rgregg/esp32-wireless-thermostat/src/controller/controller_runtime.cpp

#include "controller/controller_runtime.h"

#include <stdarg.h>
#include <stdio.h>
#include <string.h>

#include "controller/audit_log.h"
#include "espnow_cmd_word.h"
#include "mqtt_payload.h"
#include "thermostat/thermostat_state.h"

namespace {

constexpr uint32_t kOneMinuteMs = 60000;

}  // namespace

namespace thermostat {

static const char *hvac_state_str(ControllerRuntime::HvacState s) {
  switch (s) {
    case ControllerRuntime::HvacState::Idle: return "idle";
    case ControllerRuntime::HvacState::Heating: return "heating";
    case ControllerRuntime::HvacState::Cooling: return "cooling";
    default: return "?";
  }
}

void ControllerRuntime::audit(const char *fmt, ...) const {
  if (!audit_cb_) return;
  char buf[80];
  va_list ap;
  va_start(ap, fmt);
  vsnprintf(buf, sizeof(buf), fmt, ap);
  va_end(ap);
  audit_cb_(buf);
}

ControllerRuntime::ControllerRuntime(const ControllerConfig &config)
    : config_(config) {
  last_heating_off_ms_ = 0;
  last_cooling_off_ms_ = 0;
  hvac_state_since_ms_ = 0;
}

void ControllerRuntime::note_heartbeat(uint32_t now_ms) {
  heartbeat_last_seen_ms_ = now_ms;
}

void ControllerRuntime::set_hvac_lockout(bool locked_out) {
  if (locked_out != hvac_lockout_) {
    audit("lockout: %s [internal]", locked_out ? "on" : "off");
  }
  hvac_lockout_ = locked_out;
  if (hvac_lockout_) {
    hvac_state_ = HvacState::Idle;
    relay_.fan = false;
    relay_.heat = false;
    relay_.cool = false;
  }
}

void ControllerRuntime::set_windows_open(bool open) {
  if (open != windows_open_) {
    audit("windows_open: %s [internal]", open ? "on" : "off");
  }
  windows_open_ = open;
}

void ControllerRuntime::reset_remote_command_sequence() {
  last_seq_default_ = 0;
  for (int i = 0; i < kMaxCommandSources; ++i) {
    command_sources_[i].active = false;
    command_sources_[i].last_seq = 0;
  }
}

CommandApplyResult ControllerRuntime::apply_remote_command(const CommandWord &cmd,
                                                           const uint8_t *source_mac) {
  CommandApplyResult result;

  // Resolve the per-source sequence counter
  uint16_t *last_seq = &last_seq_default_;

  if (source_mac != nullptr) {
    // Find existing entry or allocate a new one
    int free_slot = -1;
    for (int i = 0; i < kMaxCommandSources; ++i) {
      if (command_sources_[i].active &&
          memcmp(command_sources_[i].mac, source_mac, 6) == 0) {
        last_seq = &command_sources_[i].last_seq;
        free_slot = -2;  // sentinel: found
        break;
      }
      if (!command_sources_[i].active && free_slot == -1) {
        free_slot = i;
      }
    }
    if (free_slot >= 0) {
      // New source — register it
      memcpy(command_sources_[free_slot].mac, source_mac, 6);
      command_sources_[free_slot].last_seq = 0;
      command_sources_[free_slot].active = true;
      last_seq = &command_sources_[free_slot].last_seq;
    } else if (free_slot == -1) {
      // All slots full and source not found — reject to avoid
      // sharing sequence tracking with the default source
      result.stale_or_duplicate = true;
      return result;
    }
  }

  if (*last_seq != 0) {
    if (!espnow_cmd::is_newer_seq(*last_seq, cmd.seq)) {
      result.stale_or_duplicate = true;
      return result;
    }
  }

  *last_seq = cmd.seq;
  result.accepted = true;

  if (cmd.sync_request) {
    result.sync_requested = true;
    return result;
  }

  const FurnaceMode old_mode = mode_;
  const FanMode old_fan = fan_mode_;
  const float old_setpoint = target_temperature_c();

  if (!cmd.preserve_mode) {
    mode_ = cmd.mode;
  }
  if (!cmd.preserve_fan) {
    fan_mode_ = cmd.fan;
  }
  // Route the incoming setpoint into the bin matching the resolved mode (the
  // mode we'll be in after applying this command). For Off, leave both bins
  // unchanged so a mode-only switch doesn't clobber the stored targets.
  // preserve_setpoint suppresses any bin update entirely.
  if (!cmd.preserve_setpoint) {
    const float incoming_sp = static_cast<float>(cmd.setpoint_decic) / 10.0f;
    const FurnaceMode bin_mode = cmd.preserve_mode ? mode_ : cmd.mode;
    if (bin_mode == FurnaceMode::Heat) {
      heat_setpoint_c_ = incoming_sp;
    } else if (bin_mode == FurnaceMode::Cool) {
      cool_setpoint_c_ = incoming_sp;
    }
  }

  // Audit changes with source MAC when available
  char src_str[32];
  if (source_mac) {
    char mac_buf[18];
    format_mac(mac_buf, sizeof(mac_buf), source_mac);
    snprintf(src_str, sizeof(src_str), "espnow %s", mac_buf);
  } else {
    strcpy(src_str, "mqtt");
  }
  if (mode_ != old_mode) {
    audit("mode: %s->%s [%s]",
          mqtt_payload::mode_to_str(old_mode),
          mqtt_payload::mode_to_str(mode_), src_str);
    // Clear sticky max-runtime flag when user changes mode (acknowledgment)
    if (max_runtime_exceeded_) {
      max_runtime_exceeded_ = false;
      audit("max_runtime: cleared by mode change [internal]");
    }
  }
  if (fan_mode_ != old_fan) {
    audit("fan: %s->%s [%s]",
          mqtt_payload::fan_to_str(old_fan),
          mqtt_payload::fan_to_str(fan_mode_), src_str);
  }
  const float new_setpoint = target_temperature_c();
  if (new_setpoint != old_setpoint) {
    audit("setpoint: %.1f->%.1f [%s]",
          static_cast<double>(old_setpoint),
          static_cast<double>(new_setpoint), src_str);
  }

  if (cmd.filter_reset) {
    filter_runtime_seconds_ = 0;
    result.filter_reset_requested = true;
    audit("filter_reset [%s]", src_str);
  }

  return result;
}

void ControllerRuntime::tick(const ControllerTickInput &in) {
  update_failsafe(in.now_ms, in.has_indoor_temp);
  apply_hvac_calls(in.now_ms, in.heat_call, in.cool_call);
  run_minute_tasks(in.now_ms);
  enforce_safety_interlocks(in.now_ms);
}

float ControllerRuntime::target_temperature_c() const {
  // Cool mode reports cool bin; Heat and Off both report heat bin.
  // Off's value is informational only — HVAC logic is gated on mode anyway.
  if (mode_ == FurnaceMode::Cool) return cool_setpoint_c_;
  return heat_setpoint_c_;
}

FurnaceStateCode ControllerRuntime::furnace_state() const {
  FurnaceStateCode base = compute_furnace_state(snapshot());
  if (equipment_delay_) {
    if (base == FurnaceStateCode::HeatMode) return FurnaceStateCode::HeatWait;
    if (base == FurnaceStateCode::CoolMode) return FurnaceStateCode::CoolWait;
  }
  return base;
}

ThermostatSnapshot ControllerRuntime::snapshot() const {
  ThermostatSnapshot s;
  s.mode = mode_;
  s.fan_mode = fan_mode_;
  s.relay = relay_;
  s.hvac_lockout = hvac_lockout_;
  s.failsafe_active = failsafe_active_;
  s.windows_open = windows_open_;
  return s;
}

void ControllerRuntime::enforce_safety_interlocks(uint32_t now_ms) {
  if (failsafe_active_ || hvac_lockout_) {
    enter_idle(now_ms);
    relay_.fan = false;
  }

  if (relay_.heat) {
    relay_.cool = false;
    relay_.fan = false;
  } else if (relay_.cool) {
    relay_.heat = false;
    relay_.fan = false;
  }
}

void ControllerRuntime::update_failsafe(uint32_t now_ms, bool has_indoor_temp) {
  const bool was_active = failsafe_active_;
  failsafe_active_ = !has_indoor_temp ||
                     is_failsafe_timed_out(now_ms, heartbeat_last_seen_ms_,
                                           config_.failsafe_timeout_ms);
  if (failsafe_active_ != was_active) {
    if (failsafe_active_) {
      audit("failsafe: on (%s) [internal]",
            !has_indoor_temp ? "no indoor temp" : "heartbeat timeout");
    } else {
      audit("failsafe: off [internal]");
    }
  }
}

void ControllerRuntime::apply_hvac_calls(uint32_t now_ms, bool heat_call, bool cool_call) {
  if (failsafe_active_ || hvac_lockout_) {
    enter_idle(now_ms);
    relay_.fan = false;
    equipment_delay_ = false;
    return;
  }

  if (windows_open_) {
    cool_call = false;
  }

  switch (hvac_state_) {
    case HvacState::Heating: {
      const bool min_run_done =
          elapsed_at_least(now_ms, hvac_state_since_ms_, config_.min_heating_run_time_ms);
      const bool max_run_exceeded =
          config_.max_heating_run_time_ms > 0 &&
          elapsed_at_least(now_ms, hvac_state_since_ms_, config_.max_heating_run_time_ms);
      if (max_run_exceeded) {
        audit("heating: max runtime exceeded, forcing idle [internal]");
        max_runtime_exceeded_ = true;
        enter_idle(now_ms);
      } else if (!heat_call && min_run_done) {
        enter_idle(now_ms);
      } else {
        relay_.heat = true;
        relay_.cool = false;
      }
      break;
    }
    case HvacState::Cooling: {
      const bool min_run_done =
          elapsed_at_least(now_ms, hvac_state_since_ms_, config_.min_cooling_run_time_ms);
      const bool max_run_exceeded =
          config_.max_cooling_run_time_ms > 0 &&
          elapsed_at_least(now_ms, hvac_state_since_ms_, config_.max_cooling_run_time_ms);
      if (max_run_exceeded) {
        audit("cooling: max runtime exceeded, forcing idle [internal]");
        max_runtime_exceeded_ = true;
        enter_idle(now_ms);
      } else if (!cool_call && min_run_done) {
        enter_idle(now_ms);
      } else {
        relay_.heat = false;
        relay_.cool = true;
      }
      break;
    }
    case HvacState::Idle:
    default: {
      const bool idle_ready = elapsed_at_least(now_ms, hvac_state_since_ms_, config_.min_idle_time_ms);
      const bool heat_off_ready =
          !has_heating_off_timestamp_ ||
          elapsed_at_least(now_ms, last_heating_off_ms_, config_.min_heating_off_time_ms);
      const bool cool_off_ready =
          !has_cooling_off_timestamp_ ||
          elapsed_at_least(now_ms, last_cooling_off_ms_, config_.min_cooling_off_time_ms);

      if (heat_call && idle_ready && heat_off_ready) {
        enter_heating(now_ms);
      } else if (cool_call && idle_ready && cool_off_ready) {
        enter_cooling(now_ms);
      } else {
        relay_.heat = false;
        relay_.cool = false;
        equipment_delay_ = (heat_call && (!idle_ready || !heat_off_ready)) ||
                           (cool_call && (!idle_ready || !cool_off_ready));
      }
      break;
    }
  }

  if (fan_mode_ == FanMode::AlwaysOn && !spare_relay_4_) {
    relay_.fan = true;
  } else if (fan_mode_ != FanMode::Circulate) {
    relay_.fan = false;
  }
}

void ControllerRuntime::run_minute_tasks(uint32_t now_ms) {
  if (last_minute_tick_ms_ == 0) {
    last_minute_tick_ms_ = now_ms;
    return;
  }

  while (elapsed_at_least(now_ms, last_minute_tick_ms_, kOneMinuteMs)) {
    last_minute_tick_ms_ += kOneMinuteMs;

    if (relay_.heat || relay_.cool || relay_.fan || spare_relay_4_) {
      filter_runtime_seconds_ += 60;
    }

    if (!failsafe_active_ && !hvac_lockout_ && fan_mode_ == FanMode::Circulate) {
      const int period = static_cast<int>(config_.fan_circulate_period_min);
      const int duration = static_cast<int>(config_.fan_circulate_duration_min);
      if (period > 0 && duration > 0) {
        ++fan_circulate_elapsed_min_;
        const bool window_open = (fan_circulate_elapsed_min_ % period) < duration;
        if (window_open && !relay_.heat && !relay_.cool && !spare_relay_4_) {
          relay_.fan = true;
        } else {
          relay_.fan = false;
        }
      }
    } else {
      fan_circulate_elapsed_min_ = 0;
    }
  }
}

bool ControllerRuntime::elapsed_at_least(uint32_t now_ms,
                                         uint32_t start_ms,
                                         uint32_t duration_ms) const {
  if (duration_ms == 0) {
    return true;
  }
  return static_cast<uint32_t>(now_ms - start_ms) >= duration_ms;
}

void ControllerRuntime::enter_idle(uint32_t now_ms) {
  if (hvac_state_ != HvacState::Idle) {
    audit("furnace: %s->idle [internal]", hvac_state_str(hvac_state_));
  }
  if (hvac_state_ == HvacState::Heating) {
    last_heating_off_ms_ = now_ms;
    has_heating_off_timestamp_ = true;
  } else if (hvac_state_ == HvacState::Cooling) {
    last_cooling_off_ms_ = now_ms;
    has_cooling_off_timestamp_ = true;
  }

  hvac_state_ = HvacState::Idle;
  hvac_state_since_ms_ = now_ms;
  relay_.heat = false;
  relay_.cool = false;
}

void ControllerRuntime::enter_heating(uint32_t now_ms) {
  audit("furnace: %s->heating [internal]", hvac_state_str(hvac_state_));
  hvac_state_ = HvacState::Heating;
  hvac_state_since_ms_ = now_ms;
  relay_.heat = true;
  relay_.cool = false;
  relay_.fan = false;
  equipment_delay_ = false;
  max_runtime_exceeded_ = false;
}

void ControllerRuntime::enter_cooling(uint32_t now_ms) {
  audit("furnace: %s->cooling [internal]", hvac_state_str(hvac_state_));
  hvac_state_ = HvacState::Cooling;
  hvac_state_since_ms_ = now_ms;
  relay_.heat = false;
  relay_.cool = true;
  relay_.fan = false;
  equipment_delay_ = false;
  max_runtime_exceeded_ = false;
}

}  // namespace thermostat
