rgregg/esp32-wireless-thermostat/src/thermostat/esp32s3_thermostat_firmware.cpp

#if defined(ARDUINO) && defined(THERMOSTAT_ROLE_THERMOSTAT)

#include "thermostat/esp32s3_thermostat_firmware.h"

#include <atomic>
#include <cctype>
#include <cmath>
#include <cstring>
#include <ctime>
#include <cstdio>

#include <Wire.h>
#include <lvgl.h>
#include <ESPmDNS.h>
#include <Preferences.h>
#include <WiFi.h>
#include "wifi_provisioning_manager.h"
#include <PubSubClient.h>
#include <WebServer.h>
#include <HTTPClient.h>
#include <WiFiClientSecure.h>
#include <esp_mac.h>
#include <esp_system.h>
#include "ota_web_updater.h"
#include "web/web_ui_escape.h"
#include "web/web_ui_shell.h"
#include "web/web_ui_fields.h"

#include "thermostat/thermostat_device_runtime.h"
#include "mqtt_payload.h"
#include "mqtt_topics.h"
#include "wifi_watchdog.h"
#include "weather_icon.h"
#include "thermostat/thermostat_screen_controller.h"
#include "thermostat/ui/thermostat_ui_shared.h"
#include "management_paths.h"
#include "device_registry.h"
#include "mac_address_utils.h"

#include <Adafruit_AHTX0.h>
#include <Adafruit_Si7021.h>

#include "esp_heap_caps.h"
#include "esp_lcd_panel_ops.h"
#include "esp_lcd_panel_rgb.h"
#include "esp_task_wdt.h"
#include "freertos/FreeRTOS.h"
#include "freertos/semphr.h"

namespace thermostat {
namespace {

constexpr int kDisplayWidth = 800;
constexpr int kDisplayHeight = 480;
constexpr uint32_t kUiTickMs = 5;
constexpr uint32_t kRuntimeTickMs = 200;
constexpr uint32_t kSensorPollMs = 60000;
constexpr uint32_t kUiRefreshMs = 500;

constexpr int kBacklightPin = 2;
// The backlight driver needs ~30 us per enable pulse to start, so ultrasonic
// PWM can't dim (25 kHz was black below ~80% duty). 800 Hz whined audibly at
// screensaver brightness; 250 Hz sits where the ear is far less sensitive.
constexpr int kBacklightFreq = 250;
constexpr int kBacklightResolution = 8;

constexpr uint8_t kGt911Addr = 0x5D;

constexpr int kTouchI2cSda = 19;
constexpr int kTouchI2cScl = 20;
constexpr int kTouchRstPin = 38;
constexpr int kSensorI2cSda = 18;
constexpr int kSensorI2cScl = 17;
constexpr uint32_t kNetworkRetryMs = 5000;
constexpr uint32_t kMqttPublishMs = 10000;
constexpr uint32_t kDisplayInitSettleMs = 150;
constexpr uint32_t kBacklightEnableDelayMs = 400;
constexpr uint32_t kRebootDelayMs = 1000;
constexpr uint32_t kRebootPanelOffDelayMs = 200;
constexpr uint32_t kIsolationRebootMs = 15UL * 60UL * 1000UL;

#ifndef THERMOSTAT_WIFI_SSID
#define THERMOSTAT_WIFI_SSID ""
#endif

#ifndef THERMOSTAT_WIFI_PASSWORD
#define THERMOSTAT_WIFI_PASSWORD ""
#endif

// ESP-NOW-only mode: when 1, the display never joins WiFi and never enters BLE
// provisioning — it brings up the LCD + ESP-NOW only. Useful for a display that
// talks solely to the controller over ESP-NOW (no WiFi infrastructure), and for
// bench validation where WiFi association would fight the pinned ESP-NOW channel.
#ifndef THERMOSTAT_WIFI_DISABLED
#define THERMOSTAT_WIFI_DISABLED 0
#endif

#ifndef THERMOSTAT_MQTT_HOST
#define THERMOSTAT_MQTT_HOST "mqtt.lan"
#endif

#ifndef THERMOSTAT_MQTT_PORT
#define THERMOSTAT_MQTT_PORT 1883
#endif

#ifndef THERMOSTAT_MQTT_USER
#define THERMOSTAT_MQTT_USER ""
#endif

#ifndef THERMOSTAT_MQTT_PASSWORD
#define THERMOSTAT_MQTT_PASSWORD ""
#endif

#ifndef THERMOSTAT_BASE_TOPIC
#define THERMOSTAT_BASE_TOPIC "esp32-wireless-thermostat"
#endif

#ifndef THERMOSTAT_MQTT_DISCOVERY_PREFIX
#define THERMOSTAT_MQTT_DISCOVERY_PREFIX "homeassistant"
#endif

#ifndef THERMOSTAT_DISPLAY_TIMEOUT_S
#define THERMOSTAT_DISPLAY_TIMEOUT_S 300
#endif

#ifndef THERMOSTAT_BACKLIGHT_ACTIVE_PCT
#define THERMOSTAT_BACKLIGHT_ACTIVE_PCT 100
#endif

#ifndef THERMOSTAT_BACKLIGHT_SCREENSAVER_PCT
#define THERMOSTAT_BACKLIGHT_SCREENSAVER_PCT 16
#endif

#ifndef THERMOSTAT_TIME_TZ
#define THERMOSTAT_TIME_TZ "PST8PDT,M3.2.0,M11.1.0"
#endif

#ifndef THERMOSTAT_TIME_NTP_1
#define THERMOSTAT_TIME_NTP_1 "0.pool.ntp.org"
#endif

#ifndef THERMOSTAT_TIME_NTP_2
#define THERMOSTAT_TIME_NTP_2 "1.pool.ntp.org"
#endif

#ifndef THERMOSTAT_TIME_NTP_3
#define THERMOSTAT_TIME_NTP_3 "2.pool.ntp.org"
#endif

#ifndef THERMOSTAT_ESPNOW_PEER_MAC
#define THERMOSTAT_ESPNOW_PEER_MAC "FF:FF:FF:FF:FF:FF"
#endif

#ifndef THERMOSTAT_ESPNOW_LMK
#define THERMOSTAT_ESPNOW_LMK "a1b2c3d4e5f60718293a4b5c6d7e8f90"
#endif

#ifndef THERMOSTAT_ESPNOW_CHANNEL
#define THERMOSTAT_ESPNOW_CHANNEL 6
#endif

#ifndef THERMOSTAT_FIRMWARE_VERSION
#define THERMOSTAT_FIRMWARE_VERSION "dev"
#endif

#ifndef THERMOSTAT_OTA_HOSTNAME
#define THERMOSTAT_OTA_HOSTNAME "esp32-furnace-thermostat"
#endif

#ifndef THERMOSTAT_OTA_PASSWORD
#define THERMOSTAT_OTA_PASSWORD ""
#endif

struct TouchState {
  bool touched = false;
  int16_t x = 0;
  int16_t y = 0;
};

uint16_t g_touch_x_max = kDisplayWidth;
uint16_t g_touch_y_max = kDisplayHeight;

esp_lcd_panel_handle_t g_panel = nullptr;
SemaphoreHandle_t g_flush_ready_sem = nullptr;
SemaphoreHandle_t g_api_mutex = nullptr;
std::atomic<bool> g_mqtt_state_dirty{false};

// Called from ISR when the panel finishes swapping framebuffers at VSYNC
bool IRAM_ATTR on_vsync_ready(esp_lcd_panel_handle_t, const esp_lcd_rgb_panel_event_data_t *,
                               void *) {
  BaseType_t high_task_wakeup = pdFALSE;
  if (g_flush_ready_sem != nullptr) {
    xSemaphoreGiveFromISR(g_flush_ready_sem, &high_task_wakeup);
  }
  return high_task_wakeup == pdTRUE;
}

lv_disp_draw_buf_t g_draw_buf;
lv_color_t *g_buf_1 = nullptr;
lv_color_t *g_buf_2 = nullptr;
lv_disp_drv_t g_disp_drv;
lv_indev_drv_t g_indev_drv;
// True once the RGB panel + LVGL display driver are fully initialized. When the
// LCD bounce-buffer allocation fails (e.g. NimBLE fragmented internal DMA RAM
// during provisioning boot), we run headless: no LVGL display/indev is registered,
// and every UI touchpoint is gated on this flag so the firmware degrades instead
// of dereferencing a null default display. Invariant: g_display_ready ⇒ g_panel
// non-null, and (after setup) g_display_ready ⇒ g_ui_ready.
// Threading: written exactly once on the main task inside init_display_and_lvgl(),
// which runs before the Core-0 web task is created (a full barrier), so no atomic
// is needed. The web task does not read this flag.
bool g_display_ready = false;

TouchState g_touch{};
enum class SensorType : uint8_t { None, AHT, Si7021 };
SensorType g_sensor_type = SensorType::None;
Adafruit_AHTX0 g_aht;
TwoWire g_touch_i2c(0);
TwoWire g_sensor_i2c(1);
Adafruit_Si7021 g_si7021(&g_sensor_i2c);
Preferences g_cfg;
bool g_cfg_ready = false;
WiFiClient g_wifi_client;
PubSubClient g_mqtt(g_wifi_client);
WebServer g_web(80);
bool g_mqtt_discovery_sent = false;
std::atomic<bool> g_web_started{false};
DeviceRegistry g_device_registry;
bool g_mdns_started = false;

ThermostatDeviceRuntime *g_runtime = nullptr;
ThermostatScreenController g_screen;

lv_obj_t *g_tabs = nullptr;
lv_obj_t *g_home_page = nullptr;
lv_obj_t *g_fan_page = nullptr;
lv_obj_t *g_mode_page = nullptr;
lv_obj_t *g_settings_page = nullptr;
lv_obj_t *g_screensaver_page = nullptr;

lv_obj_t *g_status_label = nullptr;
lv_obj_t *g_indoor_label = nullptr;
lv_obj_t *g_humidity_label = nullptr;
lv_obj_t *g_setpoint_label = nullptr;
lv_obj_t *g_outdoor_section = nullptr;
lv_obj_t *g_weather_label = nullptr;
lv_obj_t *g_weather_icon_label = nullptr;
lv_obj_t *g_home_time_label = nullptr;
lv_obj_t *g_home_date_label = nullptr;
lv_obj_t *g_screen_time_label = nullptr;
lv_obj_t *g_screen_weather_label = nullptr;
lv_obj_t *g_screen_indoor_label = nullptr;
lv_obj_t *g_screen_status_label = nullptr;
lv_obj_t *g_settings_diag_label = nullptr;
lv_obj_t *g_settings_display_label = nullptr;
lv_obj_t *g_settings_system_label = nullptr;
lv_obj_t *g_settings_wifi_label = nullptr;
lv_obj_t *g_settings_mqtt_label = nullptr;
lv_obj_t *g_settings_controller_label = nullptr;
lv_obj_t *g_settings_espnow_label = nullptr;
lv_obj_t *g_settings_config_label = nullptr;
lv_obj_t *g_settings_errors_label = nullptr;

lv_obj_t *g_setpoint_column = nullptr;
lv_obj_t *g_filter_label = nullptr;
lv_obj_t *g_fan_status_label = nullptr;
lv_obj_t *g_mode_status_label = nullptr;
lv_obj_t *g_timeout_slider = nullptr;
lv_obj_t *g_brightness_slider = nullptr;
lv_obj_t *g_dim_slider = nullptr;

uint32_t g_last_ui_tick_ms = 0;
uint32_t g_last_runtime_tick_ms = 0;
uint32_t g_last_sensor_poll_ms = 0;
uint32_t g_last_ui_refresh_ms = 0;
uint32_t g_last_mqtt_attempt_ms = 0;
uint32_t g_last_mqtt_publish_ms = 0;
uint32_t g_last_mqtt_command_ms = 0;
WifiProvisioningManager g_wifi;
float g_remote_indoor_temp_c = NAN;
float g_remote_indoor_humidity = NAN;
float g_outdoor_temp_c = 6.0f;
WeatherIcon g_weather_icon = WeatherIcon::Cloudy;
bool g_have_weather_data = false;
uint32_t g_display_timeout_ms = static_cast<uint32_t>(THERMOSTAT_DISPLAY_TIMEOUT_S) * 1000UL;
uint8_t g_cfg_backlight_active_pct = THERMOSTAT_BACKLIGHT_ACTIVE_PCT;
uint8_t g_cfg_backlight_screensaver_pct = THERMOSTAT_BACKLIGHT_SCREENSAVER_PCT;
float g_cfg_temp_comp_c = 0.0f;
bool g_cfg_temp_unit_f = false;
String g_cfg_wifi_ssid = THERMOSTAT_WIFI_SSID;
String g_cfg_wifi_password = THERMOSTAT_WIFI_PASSWORD;
bool g_cfg_wifi_disabled = THERMOSTAT_WIFI_DISABLED;  // NVS "wifi_off": ESP-NOW-only mode
String g_cfg_mqtt_host = THERMOSTAT_MQTT_HOST;
uint16_t g_cfg_mqtt_port = THERMOSTAT_MQTT_PORT;
String g_cfg_mqtt_user = THERMOSTAT_MQTT_USER;
String g_cfg_mqtt_password = THERMOSTAT_MQTT_PASSWORD;
String g_cfg_mqtt_client_id;  // derived: base_topic + "-" + device_mac
String g_cfg_base_topic = THERMOSTAT_BASE_TOPIC;
String g_cfg_discovery_prefix = THERMOSTAT_MQTT_DISCOVERY_PREFIX;
String g_cfg_device_mac;         // Full WiFi MAC "AA:BB:CC:DD:EE:FF"
String g_cfg_device_mac_compact; // Colons stripped "AABBCCDDEEFF", for MQTT/hostnames
bool g_cfg_ha_discovery_enabled = true;
String g_cfg_hostname = THERMOSTAT_OTA_HOSTNAME;
uint8_t g_cfg_espnow_channel = THERMOSTAT_ESPNOW_CHANNEL;
String g_cfg_espnow_peer_mac = THERMOSTAT_ESPNOW_PEER_MAC;
String g_cfg_espnow_lmk = THERMOSTAT_ESPNOW_LMK;
bool g_cfg_mqtt_enabled = true;    // NVS "mqtt_en"
bool g_cfg_espnow_enabled = true;  // NVS "espnow_en"

// Derived from g_cfg_espnow_peer_mac (colons stripped) — single controller MAC for both transports
String controller_mac_compact() {
  return mac_utils::mac_strip_colons(g_cfg_espnow_peer_mac);
}
uint32_t g_cfg_controller_timeout_ms = 30000;
bool g_cfg_mqtt_reconfigure_required = false;
bool g_cfg_reboot_required = false;
uint32_t g_boot_count = 0;
String g_reset_reason = "unknown";
String g_last_mqtt_error = "none";
String g_last_ota_error = "none";
String g_last_espnow_error = "none";
bool g_reboot_requested = false;
uint32_t g_reboot_at_ms = 0;
bool g_backlight_enabled = false;
uint32_t g_backlight_enable_at_ms = 0;
bool g_sensors_initialized = false;  // set true at end of init_sensors()
bool g_ui_ready = false;             // set true at end of create_ui()
uint8_t g_sensor_fail_count = 0;     // consecutive sensor read failures
uint32_t g_isolation_start_ms = 0;   // when both MQTT+ESP-NOW went down (0=not isolated)

// Shadow state for controller telemetry received via MQTT
FurnaceStateCode g_mqtt_ctrl_state = FurnaceStateCode::Error;
bool g_mqtt_ctrl_lockout = false;
bool g_mqtt_ctrl_windows_open = false;
FurnaceMode g_mqtt_ctrl_mode = FurnaceMode::Off;
FanMode g_mqtt_ctrl_fan = FanMode::Automatic;
float g_mqtt_ctrl_setpoint_c = 20.0f;
uint32_t g_mqtt_ctrl_filter_runtime_s = 0;
uint32_t g_mqtt_ctrl_last_update_ms = 0;
uint32_t g_mqtt_ctrl_last_applied_ms = 0;
bool g_mqtt_ctrl_available = false;

uint8_t clamp_percent(long value) {
  if (value < 0) {
    return 0;
  }
  if (value > 100) {
    return 100;
  }
  return static_cast<uint8_t>(value);
}

uint8_t percent_to_duty(uint8_t percent) {
  if (percent >= 100) {
    return 255;
  }
  return static_cast<uint8_t>((static_cast<uint16_t>(percent) * 255U + 50U) / 100U);
}

using mac_utils::mac_full;
using mac_utils::mac_strip_colons;

void load_runtime_config() {
  if (!g_cfg_ready) return;

  // Compute MAC-based suffix for OTA hostname default.
  String mac = mac_full();
  String mac_compact = mac_strip_colons(mac);
  mac_compact.toLowerCase();
  g_cfg_hostname = "display-" + mac_compact;

  // One-time migration: clear stale NVS keys from old config schema.
  g_cfg.remove("shared_id");
  g_cfg.remove("mqtt_cid");
  g_cfg.remove("mqtt_base");
  g_cfg.remove("ctrl_base");

  // Migrate old OTA hostname defaults.
  {
    String stored_ota = g_cfg.getString("ota_host", "");
    if (stored_ota == THERMOSTAT_OTA_HOSTNAME ||
        stored_ota == (String(THERMOSTAT_OTA_HOSTNAME) + "-000000")) {
      g_cfg.remove("ota_host");
    }
  }

  g_cfg_wifi_ssid = g_cfg.getString("wifi_ssid", g_cfg_wifi_ssid);
  g_cfg_wifi_password = g_cfg.getString("wifi_pwd", g_cfg_wifi_password);
  g_cfg_wifi_disabled = g_cfg.getBool("wifi_off", g_cfg_wifi_disabled);
  g_cfg_mqtt_host = g_cfg.getString("mqtt_host", g_cfg_mqtt_host);
  g_cfg_mqtt_port = static_cast<uint16_t>(g_cfg.getUInt("mqtt_port", g_cfg_mqtt_port));
  g_cfg_mqtt_user = g_cfg.getString("mqtt_user", g_cfg_mqtt_user);
  g_cfg_mqtt_password = g_cfg.getString("mqtt_pwd", g_cfg_mqtt_password);
  g_cfg_base_topic = g_cfg.getString("base_topic", g_cfg_base_topic);
  g_cfg_discovery_prefix = g_cfg.getString("disc_pref", g_cfg_discovery_prefix);
  g_cfg_ha_discovery_enabled = g_cfg.getBool("ha_disc", g_cfg_ha_discovery_enabled);
  g_cfg.remove("device_name");  // legacy key, hostname is now the single name
  // Migrate legacy ctrl_mac NVS key → esp_peer if esp_peer was never set
  if (g_cfg_espnow_peer_mac.length() == 0 || g_cfg_espnow_peer_mac == THERMOSTAT_ESPNOW_PEER_MAC) {
    String legacy = g_cfg.getString("ctrl_mac", "");
    if (legacy.length() > 0) {
      // ctrl_mac was stored without colons; esp_peer uses colon format
      // but mac_strip_colons handles either, so store as-is
      g_cfg_espnow_peer_mac = legacy;
      g_cfg.putString("esp_peer", legacy);
    }
  }
  g_cfg.remove("ctrl_mac"); // clean up legacy key
  g_cfg_hostname = g_cfg.getString("ota_host", g_cfg_hostname);
  g_cfg_espnow_channel = static_cast<uint8_t>(g_cfg.getUChar("esp_ch", g_cfg_espnow_channel));
  g_cfg_espnow_peer_mac = g_cfg.getString("esp_peer", g_cfg_espnow_peer_mac);
  g_cfg_espnow_lmk = g_cfg.getString("esp_lmk", g_cfg_espnow_lmk);
  g_cfg_mqtt_enabled = g_cfg.getBool("mqtt_en", true);
  g_cfg_espnow_enabled = g_cfg.getBool("espnow_en", true);
  g_cfg_controller_timeout_ms = g_cfg.getUInt("ctrl_to", g_cfg_controller_timeout_ms);
  const uint32_t display_timeout_s = g_cfg.getUInt("disp_to_s", THERMOSTAT_DISPLAY_TIMEOUT_S);
  g_display_timeout_ms = display_timeout_s * 1000UL;
  g_cfg_backlight_active_pct =
      clamp_percent(g_cfg.getUChar("bl_act", g_cfg_backlight_active_pct));
  g_cfg_backlight_screensaver_pct =
      clamp_percent(g_cfg.getUChar("bl_dim", g_cfg_backlight_screensaver_pct));
  g_cfg_temp_comp_c = g_cfg.getFloat("temp_comp", 0.0f);
  g_cfg_temp_unit_f = g_cfg.getBool("temp_u_f", false);
}

String device_topic_for(const char *mac, const char *suffix) {
  char buf[192];
  mqtt_topics::device_topic(buf, sizeof(buf), g_cfg_base_topic.c_str(), mac, suffix);
  return String(buf);
}

String self_topic_for(const char *suffix) {
  return device_topic_for(g_cfg_device_mac_compact.c_str(), suffix);
}

String controller_topic_for(const char *suffix) {
  return device_topic_for(controller_mac_compact().c_str(), suffix);
}


bool try_update_runtime_config(const String &key, const char *raw_value) {
  if (!g_cfg_ready || raw_value == nullptr) return false;
  const String value(raw_value);
  bool known = true;
#define NVS_PUT_STR(ns_key, val) \
  do { if (g_cfg.putString((ns_key), (val)) == 0) Serial.printf("[cfg] NVS write failed: %s\n", (ns_key)); } while(0)
#define NVS_PUT_UINT(ns_key, val) \
  do { if (g_cfg.putUInt((ns_key), (val)) == 0) Serial.printf("[cfg] NVS write failed: %s\n", (ns_key)); } while(0)
#define NVS_PUT_UCHAR(ns_key, val) \
  do { if (g_cfg.putUChar((ns_key), (val)) == 0) Serial.printf("[cfg] NVS write failed: %s\n", (ns_key)); } while(0)
#define NVS_PUT_FLOAT(ns_key, val) \
  do { if (g_cfg.putFloat((ns_key), (val)) == 0) Serial.printf("[cfg] NVS write failed: %s\n", (ns_key)); } while(0)
#define NVS_PUT_BOOL(ns_key, val) \
  do { if (g_cfg.putBool((ns_key), (val)) == 0) Serial.printf("[cfg] NVS write failed: %s\n", (ns_key)); } while(0)

  if (key == "wifi_ssid") {
    g_cfg_wifi_ssid = value;
    g_wifi.set_credentials(value.c_str(), g_cfg_wifi_password.c_str());
  } else if (key == "wifi_password") {
    g_cfg_wifi_password = value;
    g_wifi.set_credentials(g_cfg_wifi_ssid.c_str(), value.c_str());
  } else if (key == "mqtt_host") {
    g_cfg_mqtt_host = value;
    NVS_PUT_STR("mqtt_host", value);
    g_cfg_mqtt_reconfigure_required = true;
  } else if (key == "mqtt_port") {
    const long parsed = atol(raw_value);
    if (parsed < 1 || parsed > 65535) return false;
    g_cfg_mqtt_port = static_cast<uint16_t>(parsed);
    NVS_PUT_UINT("mqtt_port", g_cfg_mqtt_port);
    g_cfg_mqtt_reconfigure_required = true;
  } else if (key == "mqtt_user") {
    g_cfg_mqtt_user = value;
    NVS_PUT_STR("mqtt_user", value);
    g_cfg_mqtt_reconfigure_required = true;
  } else if (key == "mqtt_password") {
    g_cfg_mqtt_password = value;
    NVS_PUT_STR("mqtt_pwd", value);
    g_cfg_mqtt_reconfigure_required = true;
  } else if (key == "base_topic") {
    g_cfg_base_topic = value;
    NVS_PUT_STR("base_topic", value);
    // Recompute derived client ID
    char cid_buf[64];
    mqtt_topics::client_id(cid_buf, sizeof(cid_buf), g_cfg_base_topic.c_str(), g_cfg_device_mac_compact.c_str());
    g_cfg_mqtt_client_id = String(cid_buf);
    g_cfg_mqtt_reconfigure_required = true;
    g_mqtt_discovery_sent = false;
  } else if (key == "ha_discovery_enabled") {
    g_cfg_ha_discovery_enabled = (strcmp(raw_value, "1") == 0);
    NVS_PUT_BOOL("ha_disc", g_cfg_ha_discovery_enabled);
    g_mqtt_discovery_sent = false;
  } else if (key == "discovery_prefix") {
    g_cfg_discovery_prefix = value;
    NVS_PUT_STR("disc_pref", value);
    g_mqtt_discovery_sent = false;
  } else if (key == "display_timeout_s") {
    long seconds = atol(raw_value);
    if (seconds < 30) seconds = 30;
    if (seconds > 600) seconds = 600;
    g_display_timeout_ms = static_cast<uint32_t>(seconds) * 1000UL;
    NVS_PUT_UINT("disp_to_s", static_cast<uint32_t>(seconds));
    g_screen.set_display_timeout_ms(g_display_timeout_ms);
  } else if (key == "backlight_active_pct") {
    g_cfg_backlight_active_pct = clamp_percent(atol(raw_value));
    NVS_PUT_UCHAR("bl_act", g_cfg_backlight_active_pct);
  } else if (key == "backlight_screensaver_pct") {
    g_cfg_backlight_screensaver_pct = clamp_percent(atol(raw_value));
    NVS_PUT_UCHAR("bl_dim", g_cfg_backlight_screensaver_pct);
  } else if (key == "temp_comp_c" || key == "temp_comp") {
    float val = static_cast<float>(atof(raw_value));
    if (key == "temp_comp" && g_cfg_temp_unit_f) val = val / 1.8f;
    g_cfg_temp_comp_c = val;
    NVS_PUT_FLOAT("temp_comp", val);
    if (g_runtime != nullptr) {
      g_runtime->set_local_temperature_compensation_c(val);
    }
    g_last_sensor_poll_ms = 0;  // re-read sensor with new compensation
  } else if (key == "temperature_unit") {
    g_cfg_temp_unit_f = (value == "f" || value == "fahrenheit");
    NVS_PUT_BOOL("temp_u_f", g_cfg_temp_unit_f);
    if (g_runtime != nullptr) {
      g_runtime->set_temperature_unit(g_cfg_temp_unit_f ? TemperatureUnit::Fahrenheit
                                                        : TemperatureUnit::Celsius);
    }
    // Forward unit preference to controller on next main-loop publish
    g_mqtt_state_dirty = true;
  } else if (key == "hostname") {
    // Validate: ≤63 chars, [a-zA-Z0-9-], no leading/trailing hyphens
    if (value.length() == 0 || value.length() > 63) return false;
    if (value.charAt(0) == '-' || value.charAt(value.length() - 1) == '-') return false;
    for (unsigned i = 0; i < value.length(); ++i) {
      char c = value.charAt(i);
      if (!isalnum(c) && c != '-') return false;
    }
    g_cfg_hostname = value;
    NVS_PUT_STR("ota_host", value);
    g_mqtt_discovery_sent = false;
    g_cfg_reboot_required = true;  // WiFi/mDNS hostname only applied at boot
  } else if (key == "espnow_channel") {
    const long parsed = atol(raw_value);
    if (parsed < 1 || parsed > 14) return false;
    g_cfg_espnow_channel = static_cast<uint8_t>(parsed);
    NVS_PUT_UCHAR("esp_ch", g_cfg_espnow_channel);
    g_cfg_reboot_required = true;
  } else if (key == "espnow_peer_mac" || key == "paired_controller_mac") {
    g_cfg_espnow_peer_mac = value;
    NVS_PUT_STR("esp_peer", value);
    g_cfg_mqtt_reconfigure_required = true;
    g_cfg_reboot_required = true;
  } else if (key == "espnow_lmk") {
    g_cfg_espnow_lmk = value;
    NVS_PUT_STR("esp_lmk", value);
    g_cfg_reboot_required = true;
  } else if (key == "mqtt_enabled") {
    g_cfg_mqtt_enabled = (strcmp(raw_value, "1") == 0);
    g_cfg.putBool("mqtt_en", g_cfg_mqtt_enabled);
    if (!g_cfg_mqtt_enabled && g_mqtt.connected()) {
      g_mqtt.disconnect();
    }
    g_cfg_mqtt_reconfigure_required = true;
  } else if (key == "espnow_enabled") {
    g_cfg_espnow_enabled = (strcmp(raw_value, "1") == 0);
    g_cfg.putBool("espnow_en", g_cfg_espnow_enabled);
    g_cfg_reboot_required = true;
  } else if (key == "wifi_disabled") {
    g_cfg_wifi_disabled = (strcmp(raw_value, "1") == 0);
    g_cfg.putBool("wifi_off", g_cfg_wifi_disabled);
    g_cfg_reboot_required = true;
  } else if (key == "controller_timeout_ms") {
    const long parsed = atol(raw_value);
    if (parsed < 1000 || parsed > 600000) return false;
    g_cfg_controller_timeout_ms = static_cast<uint32_t>(parsed);
    NVS_PUT_UINT("ctrl_to", g_cfg_controller_timeout_ms);
    g_cfg_reboot_required = true;
  } else {
    known = false;
  }
  if (!known) return false;
  g_mqtt_state_dirty = true;
  return true;
}

#undef NVS_PUT_STR
#undef NVS_PUT_UINT
#undef NVS_PUT_UCHAR
#undef NVS_PUT_FLOAT
#undef NVS_PUT_BOOL

bool parse_bool_payload(const char *value) {
  return strcmp(value, "1") == 0 || strcmp(value, "true") == 0 || strcmp(value, "on") == 0;
}

void schedule_reboot() {
  g_reboot_requested = true;
  g_reboot_at_ms = millis() + kRebootDelayMs;
}

void shutdown_display_for_reboot() {
  ledcWrite(kBacklightPin, 0);
  if (g_panel != nullptr) {
    esp_lcd_panel_disp_on_off(g_panel, false);
  }
}

void lower_in_place(char *text) {
  for (size_t i = 0; text[i] != '\0'; ++i) {
    text[i] = static_cast<char>(std::tolower(static_cast<unsigned char>(text[i])));
  }
}

float parse_numeric_prefix(const std::string &text, bool *ok) {
  if (ok != nullptr) {
    *ok = false;
  }
  if (text.empty()) {
    return 0.0f;
  }
  if (!((text[0] >= '0' && text[0] <= '9') || text[0] == '-' || text[0] == '+')) {
    return 0.0f;
  }
  char *end = nullptr;
  const float value = strtof(text.c_str(), &end);
  if (end == text.c_str()) {
    return 0.0f;
  }
  if (ok != nullptr) {
    *ok = true;
  }
  return value;
}

bool json_extract_string(const String &json, const char *key, String *out, int from_index = 0) {
  if (out == nullptr || key == nullptr) return false;
  const String token = "\"" + String(key) + "\"";
  const int key_index = json.indexOf(token, from_index);
  if (key_index < 0) return false;
  const int colon_index = json.indexOf(':', key_index + token.length());
  if (colon_index < 0) return false;
  int value_start = colon_index + 1;
  while (value_start < static_cast<int>(json.length()) &&
         std::isspace(static_cast<unsigned char>(json[value_start]))) {
    ++value_start;
  }
  if (value_start >= static_cast<int>(json.length()) || json[value_start] != '"') return false;
  ++value_start;

  String value;
  bool escaped = false;
  for (int i = value_start; i < static_cast<int>(json.length()); ++i) {
    const char c = json[i];
    if (c == '"' && !escaped) {
      *out = value;
      return true;
    }
    if (escaped) {
      escaped = false;
    } else if (c == '\\') {
      escaped = true;
      continue;
    }
    value += c;
  }
  return false;
}

bool json_extract_float(const String &json, const char *key, float *out, int from_index = 0) {
  if (out == nullptr || key == nullptr) return false;
  const String token = "\"" + String(key) + "\"";
  const int key_index = json.indexOf(token, from_index);
  if (key_index < 0) return false;
  const int colon_index = json.indexOf(':', key_index + token.length());
  if (colon_index < 0) return false;
  int value_start = colon_index + 1;
  while (value_start < static_cast<int>(json.length()) &&
         std::isspace(static_cast<unsigned char>(json[value_start]))) {
    ++value_start;
  }
  if (value_start >= static_cast<int>(json.length())) return false;

  bool quoted = json[value_start] == '"';
  if (quoted) ++value_start;
  int value_end = value_start;
  while (value_end < static_cast<int>(json.length())) {
    const char c = json[value_end];
    if (quoted) {
      if (c == '"') break;
    } else if (c == ',' || c == '}' || std::isspace(static_cast<unsigned char>(c))) {
      break;
    }
    ++value_end;
  }
  if (value_end <= value_start) return false;
  *out = static_cast<float>(atof(json.substring(value_start, value_end).c_str()));
  return true;
}

void poll_weather(uint32_t now_ms) {
  if (g_runtime == nullptr) return;
  // Mark weather available if delivered via ESP-NOW (has_controller_weather)
  // or via MQTT (g_have_weather_data set in MQTT callback).
  if (g_runtime->has_controller_weather()) {
    if (g_runtime->last_controller_weather_ms() == 0)
      g_runtime->set_last_controller_weather_ms(now_ms);
    g_have_weather_data = true;
  }
}

bool parse_mac(const char *text, uint8_t out[6]) {
  if (text == nullptr || strlen(text) < 17) return false;
  unsigned values[6] = {};
  if (sscanf(text, "%02x:%02x:%02x:%02x:%02x:%02x", &values[0], &values[1], &values[2],
             &values[3], &values[4], &values[5]) != 6) {
    return false;
  }
  for (int i = 0; i < 6; ++i) out[i] = static_cast<uint8_t>(values[i] & 0xFFu);
  return true;
}

bool is_broadcast_mac(const uint8_t mac[6]) {
  static const uint8_t kBroadcast[6] = {0xFF, 0xFF, 0xFF, 0xFF, 0xFF, 0xFF};
  return memcmp(mac, kBroadcast, sizeof(kBroadcast)) == 0;
}

bool parse_lmk_hex(const char *text, uint8_t out[16]) {
  if (text == nullptr || strlen(text) != 32) return false;
  for (int i = 0; i < 16; ++i) {
    unsigned byte = 0;
    if (sscanf(text + (i * 2), "%02x", &byte) != 1) return false;
    out[i] = static_cast<uint8_t>(byte & 0xFFu);
  }
  return true;
}

const char *reset_reason_text(esp_reset_reason_t reason) {
  switch (reason) {
    case ESP_RST_POWERON:
      return "power_on";
    case ESP_RST_SW:
      return "software";
    case ESP_RST_PANIC:
      return "panic";
    case ESP_RST_INT_WDT:
      return "interrupt_wdt";
    case ESP_RST_TASK_WDT:
      return "task_wdt";
    case ESP_RST_WDT:
      return "wdt";
    case ESP_RST_DEEPSLEEP:
      return "deep_sleep";
    case ESP_RST_BROWNOUT:
      return "brownout";
    case ESP_RST_SDIO:
      return "sdio";
    default:
      return "other";
  }
}

// web_ui::html_escape() and web_ui::json_escape() are now in web_ui namespace via web_ui_escape.h

void web_handle_config_get() {
  xSemaphoreTake(g_api_mutex, portMAX_DELAY);
  String body = "{";
  body += "\"wifi_ssid\":\"" + web_ui::json_escape(g_cfg_wifi_ssid) + "\",";
  body += "\"wifi_password\":\"" + String(g_cfg_wifi_password.length() > 0 ? "set" : "unset") + "\",";
  body += "\"wifi_disabled\":" + String(g_cfg_wifi_disabled ? "true" : "false") + ",";
  body += "\"mqtt_host\":\"" + web_ui::json_escape(g_cfg_mqtt_host) + "\",";
  body += "\"mqtt_port\":" + String(g_cfg_mqtt_port) + ",";
  body += "\"mqtt_user\":\"" + web_ui::json_escape(g_cfg_mqtt_user) + "\",";
  body += "\"mqtt_password\":\"" + String(g_cfg_mqtt_password.length() > 0 ? "set" : "unset") + "\",";
  body += "\"base_topic\":\"" + web_ui::json_escape(g_cfg_base_topic) + "\",";
  body += "\"discovery_prefix\":\"" + web_ui::json_escape(g_cfg_discovery_prefix) + "\",";
  body += "\"ha_discovery_enabled\":" + String(g_cfg_ha_discovery_enabled ? "true" : "false") + ",";
  body += "\"display_timeout_s\":" + String(g_display_timeout_ms / 1000UL) + ",";
  body += "\"backlight_active_pct\":" + String(g_cfg_backlight_active_pct) + ",";
  body += "\"backlight_screensaver_pct\":" + String(g_cfg_backlight_screensaver_pct) + ",";
  body += "\"temp_comp_c\":" + String(g_cfg_temp_comp_c, 2) + ",";
  body += "\"temperature_unit\":\"" + String(g_cfg_temp_unit_f ? "f" : "c") + "\",";
  body += "\"hostname\":\"" + web_ui::json_escape(g_cfg_hostname) + "\",";
  body += "\"espnow_channel\":" + String(g_cfg_espnow_channel) + ",";
  body += "\"espnow_peer_mac\":\"" + web_ui::json_escape(g_cfg_espnow_peer_mac) + "\",";
  body += "\"espnow_lmk\":\"" + String(g_cfg_espnow_lmk.length() > 0 ? "set" : "unset") + "\",";
  body += "\"paired_controller_mac\":\"" + web_ui::json_escape(controller_mac_compact()) + "\",";
  body += "\"controller_timeout_ms\":" + String(g_cfg_controller_timeout_ms) + ",";
  body += "\"reboot_required\":" + String(g_cfg_reboot_required ? "true" : "false");
  body += "}";
  xSemaphoreGive(g_api_mutex);
  g_web.send(200, "application/json", body);
}

void web_handle_config_post() {
  int updated = 0;
  xSemaphoreTake(g_api_mutex, portMAX_DELAY);
  for (int i = 0; i < g_web.args(); ++i) {
    if (try_update_runtime_config(g_web.argName(i), g_web.arg(i).c_str())) {
      ++updated;
    }
  }
  xSemaphoreGive(g_api_mutex);
  g_web.send(200, "text/plain", "updated=" + String(updated) + "\n");
}

void web_handle_reboot_post() {
  schedule_reboot();
  g_web.send(200, "text/plain", "rebooting\n");
}

void web_handle_status_get() {
  const uint32_t now = millis();

  // Snapshot shared state under mutex before building response
  xSemaphoreTake(g_api_mutex, portMAX_DELAY);
  const uint32_t mqtt_ctrl_ms = g_mqtt_ctrl_last_update_ms;
  const uint32_t mqtt_cmd_ms = g_last_mqtt_command_ms;
  const uint32_t espnow_hb_ms = g_runtime ? g_runtime->last_controller_heartbeat_ms() : 0;
  const float remote_indoor_temp_c = g_remote_indoor_temp_c;
  const float remote_indoor_humidity = g_remote_indoor_humidity;
  const std::string indoor_temp_text = g_runtime ? g_runtime->indoor_temp_text() : std::string("");
  const std::string indoor_humidity_text = g_runtime ? g_runtime->indoor_humidity_text() : std::string("");
  const std::string setpoint_text = g_runtime ? g_runtime->setpoint_text() : std::string("");
  const std::string status_text_str = g_runtime ? g_runtime->status_text(now) : std::string("");
  const std::string weather_text_str = g_runtime ? g_runtime->weather_text() : std::string("");
  const bool have_weather = g_have_weather_data;
  const float outdoor_temp = g_outdoor_temp_c;
  const uint32_t mqtt_ctrl_applied_ms = g_mqtt_ctrl_last_applied_ms;
  const uint32_t controller_timeout = g_cfg_controller_timeout_ms;
  const String paired_ctrl_mac = controller_mac_compact();
  const FurnaceMode ctrl_mode = g_mqtt_ctrl_mode;
  const FurnaceStateCode ctrl_state = g_mqtt_ctrl_state;
  const bool ctrl_available = g_mqtt_ctrl_available;
  const SensorType sensor_type = g_sensor_type;
  const bool temp_unit_f = g_cfg_temp_unit_f;
  xSemaphoreGive(g_api_mutex);

  char buf[2048];
  // remote_indoor_temp_c is always Celsius (API contract); the unit-converted
  // value for the status page goes in remote_indoor_temp_text.
  char remote_temp_str[16], remote_temp_text[16], remote_hum_str[16];
  if (std::isnan(remote_indoor_temp_c)) {
    strcpy(remote_temp_str, "null");
    remote_temp_text[0] = '\0';
  } else {
    const double temp_c = static_cast<double>(remote_indoor_temp_c);
    snprintf(remote_temp_str, sizeof(remote_temp_str), "%.1f", temp_c);
    snprintf(remote_temp_text, sizeof(remote_temp_text), "%.1f\xc2\xb0%c",
             temp_unit_f ? temp_c * 9.0 / 5.0 + 32.0 : temp_c, temp_unit_f ? 'F' : 'C');
  }
  if (std::isnan(remote_indoor_humidity)) {
    strcpy(remote_hum_str, "null");
  } else {
    snprintf(remote_hum_str, sizeof(remote_hum_str), "%.2f", static_cast<double>(remote_indoor_humidity));
  }
  snprintf(buf, sizeof(buf),
    "{"
    "\"uptime_ms\":%lu,"
    "\"wifi_connected\":%s,"
    "\"wifi_ip\":\"%s\","
    "\"wifi_rssi\":%d,"
    "\"mqtt_connected\":%s,"
    "\"espnow_connected\":%s,"
    "\"aht_sensor_ready\":%s,"
    "\"sensor_type\":\"%s\","
    "\"remote_indoor_temp_c\":%s,"
    "\"remote_indoor_temp_text\":\"%s\","
    "\"remote_indoor_humidity\":%s,"
    "\"indoor_temp_text\":\"%s\","
    "\"indoor_humidity_text\":\"%s\","
    "\"setpoint_text\":\"%s\","
    "\"status_text\":\"%s\","
    "\"weather_text\":\"%s\","
    "\"have_weather_data\":%s,"
    "\"outdoor_temp_c\":%.1f,"
    "\"mqtt_ctrl_last_update_ms\":%lu,"
    "\"mqtt_ctrl_last_applied_ms\":%lu,"
    "\"last_mqtt_command_ms\":%lu,"
    "\"espnow_heartbeat_ms\":%lu,"
    "\"controller_timeout_ms\":%lu,"
    "\"paired_controller_mac\":\"%s\","
    "\"mqtt_ctrl_mode\":\"%s\","
    "\"mqtt_ctrl_state\":\"%s\","
    "\"mqtt_ctrl_available\":%s,"
    "\"free_heap\":%lu,"
    "\"firmware_version\":\"%s\""
    "}",
    static_cast<unsigned long>(now),
    WiFi.status() == WL_CONNECTED ? "true" : "false",
    WiFi.status() == WL_CONNECTED ? WiFi.localIP().toString().c_str() : "",
    WiFi.status() == WL_CONNECTED ? WiFi.RSSI() : 0,
    g_mqtt.connected() ? "true" : "false",
    (espnow_hb_ms > 0 && (now - espnow_hb_ms) < 30000UL) ? "true" : "false",
    sensor_type != SensorType::None ? "true" : "false",
    sensor_type == SensorType::AHT ? "aht" :
    sensor_type == SensorType::Si7021 ? "si7021" : "none",
    remote_temp_str,
    remote_temp_text,
    remote_hum_str,
    indoor_temp_text.c_str(),
    indoor_humidity_text.c_str(),
    setpoint_text.c_str(),
    status_text_str.c_str(),
    weather_text_str.c_str(),
    have_weather ? "true" : "false",
    static_cast<double>(outdoor_temp),
    static_cast<unsigned long>(mqtt_ctrl_ms),
    static_cast<unsigned long>(mqtt_ctrl_applied_ms),
    static_cast<unsigned long>(mqtt_cmd_ms),
    static_cast<unsigned long>(espnow_hb_ms),
    static_cast<unsigned long>(controller_timeout),
    paired_ctrl_mac.c_str(),
    mqtt_payload::mode_to_str(ctrl_mode),
    mqtt_payload::furnace_state_to_str(ctrl_state),
    ctrl_available ? "true" : "false",
    static_cast<unsigned long>(ESP.getFreeHeap()),
    THERMOSTAT_FIRMWARE_VERSION
  );
  g_web.send(200, "application/json", buf);
}

void write_u16_le(uint8_t *out, uint16_t value) {
  out[0] = static_cast<uint8_t>(value & 0xFFu);
  out[1] = static_cast<uint8_t>((value >> 8) & 0xFFu);
}

void write_u32_le(uint8_t *out, uint32_t value) {
  out[0] = static_cast<uint8_t>(value & 0xFFu);
  out[1] = static_cast<uint8_t>((value >> 8) & 0xFFu);
  out[2] = static_cast<uint8_t>((value >> 16) & 0xFFu);
  out[3] = static_cast<uint8_t>((value >> 24) & 0xFFu);
}

void web_handle_screenshot() {
  if (g_buf_1 == nullptr || g_buf_2 == nullptr) {
    g_web.send(503, "text/plain", "display not initialized");
    return;
  }

  // Copy the framebuffer that LVGL last finished drawing into PSRAM,
  // then stream from the snapshot — no mutex held during the slow I/O.
  const size_t frame_bytes = kDisplayWidth * kDisplayHeight * sizeof(lv_color_t);
  uint8_t *snap = static_cast<uint8_t *>(heap_caps_malloc(frame_bytes, MALLOC_CAP_SPIRAM));

  const uint16_t *fb;
  if (snap) {
    xSemaphoreTake(g_api_mutex, portMAX_DELAY);
    // buf_act is the buffer LVGL draws into next; the other holds the last complete frame
    const lv_color_t *src = (g_draw_buf.buf_act == g_buf_1) ? g_buf_2 : g_buf_1;
    memcpy(snap, src, frame_bytes);
    xSemaphoreGive(g_api_mutex);
    fb = reinterpret_cast<const uint16_t *>(snap);
  } else {
    // Fallback: stream live buffer directly (rare OOM; minor tearing acceptable)
    fb = reinterpret_cast<const uint16_t *>(
        g_draw_buf.buf_act == g_buf_1 ? g_buf_2 : g_buf_1);
  }

  const uint32_t row_size = ((kDisplayWidth * 3U) + 3U) & ~3U;
  const uint32_t image_size = row_size * kDisplayHeight;
  const uint32_t file_size = 54U + image_size;

  g_web.setContentLength(file_size);
  g_web.send(200, "image/bmp", "");
  WiFiClient client = g_web.client();

  uint8_t header[54] = {0};
  header[0] = 'B';
  header[1] = 'M';
  write_u32_le(&header[2], file_size);
  write_u32_le(&header[10], 54U);
  write_u32_le(&header[14], 40U);
  write_u32_le(&header[18], static_cast<uint32_t>(kDisplayWidth));
  write_u32_le(&header[22], static_cast<uint32_t>(kDisplayHeight));
  write_u16_le(&header[26], 1U);
  write_u16_le(&header[28], 24U);
  write_u32_le(&header[34], image_size);
  client.write(header, sizeof(header));

  static uint8_t row[((kDisplayWidth * 3U) + 3U) & ~3U];
  for (int y = kDisplayHeight - 1; y >= 0; --y) {
    uint32_t idx = 0;
    for (int x = 0; x < kDisplayWidth; ++x) {
      const uint16_t px = fb[(y * kDisplayWidth) + x];
      const uint8_t r = static_cast<uint8_t>(((px >> 11) & 0x1F) * 255 / 31);
      const uint8_t g = static_cast<uint8_t>(((px >> 5) & 0x3F) * 255 / 63);
      const uint8_t b = static_cast<uint8_t>((px & 0x1F) * 255 / 31);
      row[idx++] = b;
      row[idx++] = g;
      row[idx++] = r;
    }
    while (idx < row_size) {
      row[idx++] = 0;
    }
    client.write(row, row_size);
  }

  if (snap) {
    heap_caps_free(snap);
  }
}

void web_handle_devices_get() {
  xSemaphoreTake(g_api_mutex, portMAX_DELAY);
  DeviceRegistry snapshot = g_device_registry;
  xSemaphoreGive(g_api_mutex);

  String json = "[";
  bool first = true;
  for (size_t i = 0; i < kMaxRegistryEntries; ++i) {
    const auto &e = snapshot.entries[i];
    if (!e.occupied) continue;
    if (!first) json += ',';
    first = false;
    json += "{\"mac\":\"";
    json += web_ui::json_escape(e.mac);
    json += "\",\"name\":\"";
    json += web_ui::json_escape(e.name);
    json += "\",\"type\":\"";
    json += web_ui::json_escape(e.type);
    json += "\",\"ip\":\"";
    json += web_ui::json_escape(e.ip);
    json += "\"}";
  }
  json += "]";
  g_web.send(200, "application/json", json);
}

void web_handle_root() {
  using namespace web_ui;

  // Snapshot config globals under mutex (brief hold), then build HTML outside
  xSemaphoreTake(g_api_mutex, portMAX_DELAY);
  const String ota_hostname = g_cfg_hostname;
  const bool reboot_required = g_cfg_reboot_required;
  const String wifi_ssid = g_cfg_wifi_ssid;
  const bool wifi_pwd_set = g_cfg_wifi_password.length() > 0;
  const String mqtt_host = g_cfg_mqtt_host;
  const uint16_t mqtt_port = g_cfg_mqtt_port;
  const String mqtt_user = g_cfg_mqtt_user;
  const bool mqtt_pwd_set = g_cfg_mqtt_password.length() > 0;
  const String base_topic = g_cfg_base_topic;
  const bool ha_disc_enabled = g_cfg_ha_discovery_enabled;
  const String paired_ctrl_mac = controller_mac_compact();
  const String disc_prefix = g_cfg_discovery_prefix;
  const uint8_t espnow_channel = g_cfg_espnow_channel;
  const String espnow_peer_mac = g_cfg_espnow_peer_mac;
  const bool espnow_lmk_set = g_cfg_espnow_lmk.length() > 0;
  const uint32_t display_timeout_s = g_display_timeout_ms / 1000UL;
  const uint8_t bl_active = g_cfg_backlight_active_pct;
  const uint8_t bl_saver = g_cfg_backlight_screensaver_pct;
  const bool temp_unit_f = g_cfg_temp_unit_f;
  const float temp_comp = g_cfg_temp_comp_c;
  const uint32_t ctrl_timeout = g_cfg_controller_timeout_ms;
  const bool mqtt_enabled = g_cfg_mqtt_enabled;
  const bool espnow_enabled = g_cfg_espnow_enabled;
  xSemaphoreGive(g_api_mutex);

  String html;
  html.reserve(12288);

  static const TabDef tabs[] = {
    {"status", "Status"},
    {"wifi", "WiFi"},
    {"mqtt", "MQTT"},
    {"display", "Display"},
    {"hw", "Hardware"},
    {"system", "System"},
  };
  page_begin(html, "Thermostat Display", ota_hostname.c_str(),
             tabs, sizeof(tabs) / sizeof(tabs[0]));

  // ── Status tab ──
  tab_begin(html, "status", true);
  card_begin(html, "Display Status");
  status_grid_begin(html);
  status_section(html, "Connectivity");
  status_item(html, "WiFi", "wifi_connected");
  status_item(html, "IP Address", "wifi_ip");
  status_item(html, "RSSI", "wifi_rssi");
  status_item(html, "MQTT", "mqtt_connected");
  status_item(html, "ESP-NOW", "espnow_connected");
  status_section(html, "Environment");
  status_item(html, "Sensor", "sensor_type");
  status_item(html, "Remote Temp", "remote_indoor_temp_text");
  status_item(html, "Remote Humidity", "remote_indoor_humidity");
  status_item(html, "Indoor Temp", "indoor_temp_text");
  status_item(html, "Indoor Humidity", "indoor_humidity_text");
  status_item(html, "Setpoint", "setpoint_text");
  status_item(html, "Weather", "weather_text");
  status_section(html, "Controller");
  status_item(html, "Status", "status_text");
  status_item(html, "Mode", "mqtt_ctrl_mode");
  status_item(html, "State", "mqtt_ctrl_state");
  status_item(html, "Available", "mqtt_ctrl_available");
  status_section(html, "System");
  status_item(html, "Free Heap", "free_heap");
  status_item(html, "Uptime", "uptime_ms");
  status_item(html, "Firmware", "firmware_version");
  status_grid_end(html);
  card_end(html);
  if (reboot_required) {
    html += F("<div class=\"card\" style=\"border:1px solid var(--wn)\">"
              "<p style=\"color:var(--wn)\">Reboot required for pending changes.</p></div>");
  }
  tab_end(html);

  // ── WiFi tab ──
  tab_begin(html, "wifi");
  card_begin(html, "WiFi Settings");
  form_begin(html);
  text_field(html, "WiFi SSID", "wifi_ssid", wifi_ssid, nullptr, nullptr, nullptr, 64);
  password_field(html, "WiFi Password", "wifi_password", wifi_pwd_set);
  form_end(html, "Save WiFi");
  card_end(html);
  tab_end(html);

  // ── MQTT tab ──
  tab_begin(html, "mqtt");
  card_begin(html, "MQTT Broker");
  form_begin(html);
  text_field(html, "Broker Host", "mqtt_host", mqtt_host);
  number_field(html, "Broker Port", "mqtt_port", String(mqtt_port), "1", "65535", "1");
  text_field(html, "Username", "mqtt_user", mqtt_user);
  password_field(html, "Password", "mqtt_password", mqtt_pwd_set);
  text_field(html, "Base Topic", "base_topic", base_topic,
             "e.g. esp32-wireless-thermostat");
  checkbox_field(html, "HA Discovery", "ha_discovery_enabled", ha_disc_enabled,
                 "ha-disc-opts");
  html += F("<div id=\"ha-disc-opts\"");
  if (!ha_disc_enabled) html += F(" style=\"display:none\"");
  html += F(">");
  text_field(html, "Discovery Prefix", "discovery_prefix", disc_prefix,
             "HA MQTT discovery prefix, e.g. homeassistant");
  html += F("</div>");
  form_end(html, "Save MQTT");
  card_end(html);
  tab_end(html);

  // ── Display tab ──
  tab_begin(html, "display");
  card_begin(html, "Screen Settings");
  form_begin(html);
  number_field(html, "Screen Timeout (seconds)", "display_timeout_s",
               String(display_timeout_s), "30", "600", "1");
  number_field(html, "Active Brightness (%)", "backlight_active_pct",
               String(bl_active), "0", "100", "1");
  number_field(html, "Screensaver Brightness (%)", "backlight_screensaver_pct",
               String(bl_saver), "0", "100", "1");
  {
    static const SelectOption temp_opts[] = {{"c", "Celsius"}, {"f", "Fahrenheit"}};
    select_field(html, "Temperature Unit", "temperature_unit",
                 temp_opts, 2, String(temp_unit_f ? "f" : "c"));
  }
  form_end(html, "Save Display");
  card_end(html);
  tab_end(html);

  // ── Hardware tab ──
  tab_begin(html, "hw");

  // Device card
  card_begin(html, "Device");
  form_begin(html);
  text_field(html, "Hostname", "hostname", ota_hostname,
             "Used for mDNS, DHCP, and MQTT device name",
             "^[a-zA-Z0-9]([a-zA-Z0-9-]*[a-zA-Z0-9])?$",
             "Letters, digits, hyphens; max 63 chars", 63);
  form_end(html, "Save");
  card_end(html);

  // Controller card
  card_begin(html, "Controller");
  form_begin(html);
  mac_field(html, "Controller MAC", "espnow_peer_mac", espnow_peer_mac);
  form_end(html, "Save");
  card_end(html);

  // Transport card
  card_begin(html, "Transport");
  form_begin(html);
  checkbox_field(html, "Enable MQTT", "mqtt_enabled", mqtt_enabled);
  checkbox_field(html, "Enable ESP-NOW", "espnow_enabled", espnow_enabled);
  form_end(html, "Save");
  card_end(html);

  // ESP-NOW Settings card
  card_begin(html, "ESP-NOW Settings");
  form_begin(html);
  number_field(html, "Channel", "espnow_channel", String(espnow_channel), "1", "14", "1");
  password_field(html, "Encryption Key (LMK)", "espnow_lmk",
                 espnow_lmk_set,
                 "^[0-9A-Fa-f]{32}$", "32 hex characters");
  form_end(html, "Save ESP-NOW");
  card_end(html);

  // Sensor card
  card_begin(html, "Sensor");
  form_begin(html);
  {
    float comp_display = temp_unit_f ? temp_comp * 1.8f : temp_comp;
    number_field(html, temp_unit_f ? "Temp Compensation (\xc2\xb0""F)" : "Temp Compensation (\xc2\xb0""C)",
                 "temp_comp", String(comp_display, 2),
                 temp_unit_f ? "-18" : "-10", temp_unit_f ? "18" : "10", "0.01",
                 "Offset applied to AHT sensor readings");
  }
  number_field(html, "Controller Timeout (ms)", "controller_timeout_ms",
               String(ctrl_timeout), "1000", "600000", "1",
               "Time before controller is considered disconnected");
  form_end(html, "Save");
  card_end(html);

  tab_end(html);

  // ── System tab ──
  tab_begin(html, "system");
  card_begin(html, "Firmware Update");
  html += F("<form method=\"post\" action=\"/update\" enctype=\"multipart/form-data\">");
  file_upload(html);
  html += F("<div class=\"mt\"><button type=\"submit\" class=\"btn btn-p\">Upload Firmware</button></div>");
  html += F("</form>");
  card_end(html);

  card_begin(html, "Device Control");
  reboot_button(html, "Reboot Display");
  card_end(html);

  card_begin(html, "Screenshot");
  html += F("<p><img id=\"scr\" data-src=\"/screenshot\" style=\"max-width:100%;border-radius:0.375rem\"></p>");
  card_end(html);

  card_begin(html, "Links");
  html += F("<p style=\"font-size:0.85rem\"><a href=\"/config\" style=\"color:var(--ac)\">JSON Config</a>"
            " &middot; <a href=\"/status\" style=\"color:var(--ac)\">JSON Status</a>"
            " &middot; <a href=\"/screenshot\" style=\"color:var(--ac)\">Screenshot (BMP)</a></p>");
  card_end(html);
  tab_end(html);

  page_end(html);
  g_web.send(200, "text/html", html);
}

static void web_server_task(void *) {
  // Wait for the web server to be configured and started.
  // Use a longer delay to minimise Core 0 contention during WiFi connect.
  while (!g_web_started) {
    vTaskDelay(pdMS_TO_TICKS(500));
  }
  while (true) {
    g_web.handleClient();
    ota_web_loop();
    vTaskDelay(pdMS_TO_TICKS(5));
  }
}

void ensure_web_ready() {
  if (WiFi.status() != WL_CONNECTED) return;
  if (!g_web_started) {
    g_web.on("/", HTTP_GET, web_handle_root);
    g_web.on("/status", HTTP_GET, web_handle_status_get);
    g_web.on("/devices", HTTP_GET, web_handle_devices_get);
    g_web.on("/config", HTTP_GET, web_handle_config_get);
    g_web.on("/config", HTTP_POST, web_handle_config_post);
    g_web.on("/reboot", HTTP_POST, web_handle_reboot_post);
    g_web.on("/screenshot", HTTP_GET, web_handle_screenshot);
    ota_web_setup(g_web);
    ota_set_prepare_callback([]() {
      // Close the MQTT TCP socket immediately to free ~5-6KB of internal SRAM
      // socket buffers before any OTA data arrives.  We call stop() on the
      // raw WiFiClient (lwip socket close) rather than PubSubClient::disconnect()
      // which is not thread-safe across cores.  The main loop does full teardown.
      g_wifi_client.stop();
      Serial.printf("[ota] prepare: closed MQTT socket, heap=%u internal=%u\n",
                    ESP.getFreeHeap(),
                    heap_caps_get_free_size(MALLOC_CAP_INTERNAL));
    });
    g_web.begin();
    g_web_started = true;
  }
}

std::string current_time_text() {
  time_t now = time(nullptr);
  if (now < 1700000000L) {
    return "--:--";
  }
  struct tm local_tm {};
  localtime_r(&now, &local_tm);
  char buf[24];
  strftime(buf, sizeof(buf), "%I:%M %p", &local_tm);
  return std::string(buf[0] == '0' ? buf + 1 : buf);
}

std::string current_date_text() {
  time_t now = time(nullptr);
  if (now < 1700000000L) {
    return "--- date ---";
  }
  struct tm local_tm {};
  localtime_r(&now, &local_tm);
  char buf[32];
  strftime(buf, sizeof(buf), "%A, %b %d", &local_tm);
  return std::string(buf);
}

void mqtt_publish_state() {
  if (g_runtime == nullptr || !g_mqtt.connected()) return;

  const uint32_t now = millis();

  g_mqtt.publish(self_topic_for("state/availability").c_str(), "online", true);
  g_mqtt.publish(self_topic_for("state/mode").c_str(), mqtt_payload::mode_to_str(g_runtime->local_mode()), true);
  g_mqtt.publish(self_topic_for("state/fan_mode").c_str(), mqtt_payload::fan_to_str(g_runtime->local_fan_mode()),
                 true);

  char buf[32];
  snprintf(buf, sizeof(buf), "%.1f", g_runtime->local_setpoint_c());
  g_mqtt.publish(self_topic_for("state/target_temp_c").c_str(), buf, true);
  if (g_runtime->has_last_packed_command()) {
    snprintf(buf, sizeof(buf), "%lu",
             static_cast<unsigned long>(g_runtime->last_packed_command()));
    g_mqtt.publish(self_topic_for("state/packed_command").c_str(), buf, false);
    snprintf(buf, sizeof(buf), "%u", static_cast<unsigned>(g_runtime->last_command_seq()));
    g_mqtt.publish(self_topic_for("state/command_seq").c_str(), buf, false);
  }

  snprintf(buf, sizeof(buf), "%.2f", g_runtime->local_temperature_compensation_c());
  g_mqtt.publish(self_topic_for("state/temp_comp_c").c_str(), buf, true);
  snprintf(buf, sizeof(buf), "%lu", static_cast<unsigned long>(g_display_timeout_ms / 1000UL));
  g_mqtt.publish(self_topic_for("state/display_timeout_s").c_str(), buf, true);
  snprintf(buf, sizeof(buf), "%u", static_cast<unsigned>(g_cfg_backlight_active_pct));
  g_mqtt.publish(self_topic_for("state/backlight_active_pct").c_str(), buf, true);
  snprintf(buf, sizeof(buf), "%u", static_cast<unsigned>(g_cfg_backlight_screensaver_pct));
  g_mqtt.publish(self_topic_for("state/backlight_screensaver_pct").c_str(), buf, true);
  g_mqtt.publish(self_topic_for("state/firmware_version").c_str(), THERMOSTAT_FIRMWARE_VERSION, true);
  snprintf(buf, sizeof(buf), "%lu", static_cast<unsigned long>(g_boot_count));
  g_mqtt.publish(self_topic_for("state/boot_count").c_str(), buf, true);
  g_mqtt.publish(self_topic_for("state/reset_reason").c_str(), g_reset_reason.c_str(), true);
  snprintf(buf, sizeof(buf), "%lu", static_cast<unsigned long>(millis() / 1000UL));
  g_mqtt.publish(self_topic_for("state/uptime_s").c_str(), buf, true);
  snprintf(buf, sizeof(buf), "%lu", static_cast<unsigned long>(g_last_mqtt_command_ms));
  g_mqtt.publish(self_topic_for("state/last_mqtt_command_ms").c_str(), buf, true);
  snprintf(buf, sizeof(buf), "%lu",
           static_cast<unsigned long>(g_runtime->last_controller_heartbeat_ms()));
  g_mqtt.publish(self_topic_for("state/last_espnow_rx_ms").c_str(), buf, true);
  snprintf(buf, sizeof(buf), "%lu",
           static_cast<unsigned long>(g_runtime->espnow_send_ok_count()));
  g_mqtt.publish(self_topic_for("state/espnow_send_ok_count").c_str(), buf, true);
  snprintf(buf, sizeof(buf), "%lu",
           static_cast<unsigned long>(g_runtime->espnow_send_fail_count()));
  g_mqtt.publish(self_topic_for("state/espnow_send_fail_count").c_str(), buf, true);
  if (g_last_espnow_error != "begin_failed") {
    g_last_espnow_error = g_runtime->espnow_send_fail_count() > 0 ? "send_failed" : "none";
  }
  snprintf(buf, sizeof(buf), "%lu",
           static_cast<unsigned long>(esp_get_free_heap_size()));
  g_mqtt.publish(self_topic_for("state/free_heap_bytes").c_str(), buf, true);
  g_mqtt.publish(self_topic_for("state/error_mqtt").c_str(), g_last_mqtt_error.c_str(), true);
  g_mqtt.publish(self_topic_for("state/error_ota").c_str(), g_last_ota_error.c_str(), true);
  g_mqtt.publish(self_topic_for("state/error_espnow").c_str(), g_last_espnow_error.c_str(), true);

  {
    const uint32_t now_ms = millis();
    const uint32_t mqtt_ms = std::max(g_last_mqtt_command_ms, g_mqtt_ctrl_last_update_ms);
    const uint32_t espnow_ms = g_runtime->last_controller_heartbeat_ms();
    const bool mqtt_active = mqtt_ms > 0 && (now_ms - mqtt_ms) < g_cfg_controller_timeout_ms;
    const bool espnow_active = espnow_ms > 0 && (now_ms - espnow_ms) < g_cfg_controller_timeout_ms;
    const char *path = espnow_active && mqtt_active ? "mqtt+esp-now"
                       : mqtt_active                ? "mqtt"
                       : espnow_active              ? "esp-now"
                                                    : "disconnected";
    g_mqtt.publish(self_topic_for("state/connection_path").c_str(), path, true);
  }

  if (WiFi.status() == WL_CONNECTED) {
    g_mqtt.publish(self_topic_for("state/wifi_ip").c_str(), WiFi.localIP().toString().c_str(), true);
    g_mqtt.publish(self_topic_for("state/wifi_mac").c_str(), WiFi.macAddress().c_str(), true);
    g_mqtt.publish(self_topic_for("state/wifi_ssid").c_str(), WiFi.SSID().c_str(), true);
    snprintf(buf, sizeof(buf), "%d", WiFi.channel());
    g_mqtt.publish(self_topic_for("state/wifi_channel").c_str(), buf, true);
    snprintf(buf, sizeof(buf), "%d", WiFi.RSSI());
    g_mqtt.publish(self_topic_for("state/wifi_rssi").c_str(), buf, true);
  }

  const float indoor_c = g_runtime->local_indoor_temperature_c();
  const bool ok_temp = std::isfinite(indoor_c);
  if (ok_temp) {
    snprintf(buf, sizeof(buf), "%.2f", indoor_c);
    g_mqtt.publish(self_topic_for("state/current_temp_c").c_str(), buf, true);
  }

  const float indoor_h = g_runtime->local_indoor_humidity();
  const bool ok_humidity = std::isfinite(indoor_h);
  if (ok_humidity) {
    snprintf(buf, sizeof(buf), "%.2f", indoor_h);
    g_mqtt.publish(self_topic_for("state/current_humidity").c_str(), buf, true);
  }

  // Publish local sensor data under own device path.
  if (g_sensor_type != SensorType::None) {
    if (ok_temp) {
      snprintf(buf, sizeof(buf), "%.2f", indoor_c);
      g_mqtt.publish(self_topic_for("sensor/temp_c").c_str(), buf, false);
    }
    if (ok_humidity) {
      snprintf(buf, sizeof(buf), "%.2f", indoor_h);
      g_mqtt.publish(self_topic_for("sensor/humidity").c_str(), buf, false);
    }
  }

  g_mqtt.publish(self_topic_for("state/status").c_str(), g_runtime->status_text(now).c_str(), true);
}

void mqtt_publish_discovery() {
  if (!g_mqtt.connected() || g_mqtt_discovery_sent) return;

  const String base = g_cfg_base_topic + "/devices/" + g_cfg_device_mac_compact;
  const String node = g_cfg_base_topic + "_" + g_cfg_device_mac_compact + "_display";

  // Climate entity is now published by the controller. Display publishes only
  // display-specific entities (timeout, brightness, diagnostics).

  char payload[1500];
  const String timeout_config = g_cfg_discovery_prefix + "/number/" + node +
                                "_display_timeout/config";
  snprintf(payload, sizeof(payload),
           "{\"name\":\"Display Timeout\",\"uniq_id\":\"%s_display_timeout\","
           "\"cmd_t\":\"%s/cmd/display_timeout_s\",\"stat_t\":\"%s/state/display_timeout_s\","
           "\"min\":30,\"max\":600,\"step\":5,\"mode\":\"box\",\"unit_of_meas\":\"s\","
           "\"entity_category\":\"config\",\"dev\":{\"ids\":[\"%s\"],\"name\":\"%s\","
           "\"mf\":\"rgregg\",\"mdl\":\"ESP32 Thermostat\"}}",
           node.c_str(), base.c_str(), base.c_str(), node.c_str(),
           g_cfg_hostname.c_str());
  g_mqtt.publish(timeout_config.c_str(), payload, true);

  const String brightness_config = g_cfg_discovery_prefix + "/number/" + node +
                                   "_display_backlight_active/config";
  snprintf(payload, sizeof(payload),
           "{\"name\":\"Display Brightness\",\"uniq_id\":\"%s_display_backlight_active\","
           "\"cmd_t\":\"%s/cmd/backlight_active_pct\","
           "\"stat_t\":\"%s/state/backlight_active_pct\","
           "\"min\":0,\"max\":100,\"step\":1,\"mode\":\"box\",\"unit_of_meas\":\"%%\","
           "\"entity_category\":\"config\",\"dev\":{\"ids\":[\"%s\"]}}",
           node.c_str(), base.c_str(), base.c_str(), node.c_str());
  g_mqtt.publish(brightness_config.c_str(), payload, true);

  const String dim_brightness_config = g_cfg_discovery_prefix + "/number/" + node +
                                       "_display_backlight_screensaver/config";
  snprintf(payload, sizeof(payload),
           "{\"name\":\"Screensaver Brightness\","
           "\"uniq_id\":\"%s_display_backlight_screensaver\","
           "\"cmd_t\":\"%s/cmd/backlight_screensaver_pct\","
           "\"stat_t\":\"%s/state/backlight_screensaver_pct\","
           "\"min\":0,\"max\":100,\"step\":1,\"mode\":\"box\",\"unit_of_meas\":\"%%\","
           "\"entity_category\":\"config\",\"dev\":{\"ids\":[\"%s\"]}}",
           node.c_str(), base.c_str(), base.c_str(), node.c_str());
  g_mqtt.publish(dim_brightness_config.c_str(), payload, true);

  const String fw_config = g_cfg_discovery_prefix + "/sensor/" + node + "_firmware/config";
  snprintf(payload, sizeof(payload),
           "{\"name\":\"Firmware Version\",\"uniq_id\":\"%s_firmware\",\"stat_t\":\"%s/state/firmware_version\","
           "\"entity_category\":\"diagnostic\",\"dev\":{\"ids\":[\"%s\"]}}",
           node.c_str(), base.c_str(), node.c_str());
  g_mqtt.publish(fw_config.c_str(), payload, true);

  const String rssi_config =
      g_cfg_discovery_prefix + "/sensor/" + node + "_display_wifi_rssi/config";
  snprintf(payload, sizeof(payload),
           "{\"name\":\"Display WiFi RSSI\",\"uniq_id\":\"%s_display_wifi_rssi\","
           "\"stat_t\":\"%s/state/wifi_rssi\",\"unit_of_meas\":\"dBm\","
           "\"dev_cla\":\"signal_strength\",\"stat_cla\":\"measurement\","
           "\"entity_category\":\"diagnostic\",\"en\":false,\"dev\":{\"ids\":[\"%s\"]}}",
           node.c_str(), base.c_str(), node.c_str());
  g_mqtt.publish(rssi_config.c_str(), payload, true);

  const String ip_config =
      g_cfg_discovery_prefix + "/sensor/" + node + "_display_ip/config";
  snprintf(payload, sizeof(payload),
           "{\"name\":\"Display IP Address\",\"uniq_id\":\"%s_display_ip\","
           "\"stat_t\":\"%s/state/wifi_ip\",\"icon\":\"mdi:ip-network\","
           "\"entity_category\":\"diagnostic\",\"dev\":{\"ids\":[\"%s\"]}}",
           node.c_str(), base.c_str(), node.c_str());
  g_mqtt.publish(ip_config.c_str(), payload, true);

  const String conn_path_config =
      g_cfg_discovery_prefix + "/sensor/" + node + "_display_connection_path/config";
  snprintf(payload, sizeof(payload),
           "{\"name\":\"Display Connection Path\",\"uniq_id\":\"%s_display_connection_path\","
           "\"stat_t\":\"%s/state/connection_path\",\"icon\":\"mdi:connection\","
           "\"entity_category\":\"diagnostic\",\"dev\":{\"ids\":[\"%s\"]}}",
           node.c_str(), base.c_str(), node.c_str());
  g_mqtt.publish(conn_path_config.c_str(), payload, true);

  const String heap_config =
      g_cfg_discovery_prefix + "/sensor/" + node + "_display_free_heap/config";
  snprintf(payload, sizeof(payload),
           "{\"name\":\"Display Free Heap\",\"uniq_id\":\"%s_display_free_heap\","
           "\"stat_t\":\"%s/state/free_heap_bytes\",\"unit_of_meas\":\"B\","
           "\"entity_category\":\"diagnostic\",\"en\":false,\"dev\":{\"ids\":[\"%s\"]}}",
           node.c_str(), base.c_str(), node.c_str());
  g_mqtt.publish(heap_config.c_str(), payload, true);

  const String last_mqtt_cmd_config =
      g_cfg_discovery_prefix + "/sensor/" + node + "_display_last_mqtt_command/config";
  snprintf(payload, sizeof(payload),
           "{\"name\":\"Display Last MQTT Command\",\"uniq_id\":\"%s_display_last_mqtt_command\","
           "\"stat_t\":\"%s/state/last_mqtt_command_ms\",\"unit_of_meas\":\"ms\","
           "\"entity_category\":\"diagnostic\",\"en\":false,\"dev\":{\"ids\":[\"%s\"]}}",
           node.c_str(), base.c_str(), node.c_str());
  g_mqtt.publish(last_mqtt_cmd_config.c_str(), payload, true);

  const String last_espnow_rx_config =
      g_cfg_discovery_prefix + "/sensor/" + node + "_display_last_espnow_rx/config";
  snprintf(payload, sizeof(payload),
           "{\"name\":\"Display Last ESP-NOW RX\",\"uniq_id\":\"%s_display_last_espnow_rx\","
           "\"stat_t\":\"%s/state/last_espnow_rx_ms\",\"unit_of_meas\":\"ms\","
           "\"entity_category\":\"diagnostic\",\"en\":false,\"dev\":{\"ids\":[\"%s\"]}}",
           node.c_str(), base.c_str(), node.c_str());
  g_mqtt.publish(last_espnow_rx_config.c_str(), payload, true);

  const String espnow_ok_config =
      g_cfg_discovery_prefix + "/sensor/" + node + "_display_espnow_send_ok/config";
  snprintf(payload, sizeof(payload),
           "{\"name\":\"Display ESP-NOW Send OK\",\"uniq_id\":\"%s_display_espnow_send_ok\","
           "\"stat_t\":\"%s/state/espnow_send_ok_count\",\"icon\":\"mdi:counter\","
           "\"entity_category\":\"diagnostic\",\"en\":false,\"dev\":{\"ids\":[\"%s\"]}}",
           node.c_str(), base.c_str(), node.c_str());
  g_mqtt.publish(espnow_ok_config.c_str(), payload, true);

  const String espnow_fail_config =
      g_cfg_discovery_prefix + "/sensor/" + node + "_display_espnow_send_fail/config";
  snprintf(payload, sizeof(payload),
           "{\"name\":\"Display ESP-NOW Send Fail\",\"uniq_id\":\"%s_display_espnow_send_fail\","
           "\"stat_t\":\"%s/state/espnow_send_fail_count\",\"icon\":\"mdi:counter\","
           "\"entity_category\":\"diagnostic\",\"en\":false,\"dev\":{\"ids\":[\"%s\"]}}",
           node.c_str(), base.c_str(), node.c_str());
  g_mqtt.publish(espnow_fail_config.c_str(), payload, true);

  const String err_mqtt_config =
      g_cfg_discovery_prefix + "/sensor/" + node + "_display_error_mqtt/config";
  snprintf(payload, sizeof(payload),
           "{\"name\":\"Display MQTT Error\",\"uniq_id\":\"%s_display_error_mqtt\","
           "\"stat_t\":\"%s/state/error_mqtt\",\"entity_category\":\"diagnostic\","
           "\"dev\":{\"ids\":[\"%s\"]}}",
           node.c_str(), base.c_str(), node.c_str());
  g_mqtt.publish(err_mqtt_config.c_str(), payload, true);

  const String err_ota_config =
      g_cfg_discovery_prefix + "/sensor/" + node + "_display_error_ota/config";
  snprintf(payload, sizeof(payload),
           "{\"name\":\"Display OTA Error\",\"uniq_id\":\"%s_display_error_ota\","
           "\"stat_t\":\"%s/state/error_ota\",\"entity_category\":\"diagnostic\","
           "\"dev\":{\"ids\":[\"%s\"]}}",
           node.c_str(), base.c_str(), node.c_str());
  g_mqtt.publish(err_ota_config.c_str(), payload, true);

  const String err_espnow_config =
      g_cfg_discovery_prefix + "/sensor/" + node + "_display_error_espnow/config";
  snprintf(payload, sizeof(payload),
           "{\"name\":\"Display ESP-NOW Error\",\"uniq_id\":\"%s_display_error_espnow\","
           "\"stat_t\":\"%s/state/error_espnow\",\"entity_category\":\"diagnostic\","
           "\"dev\":{\"ids\":[\"%s\"]}}",
           node.c_str(), base.c_str(), node.c_str());
  g_mqtt.publish(err_espnow_config.c_str(), payload, true);

  const String reset_seq_config =
      g_cfg_discovery_prefix + "/button/" + node + "_display_reset_sequence/config";
  snprintf(payload, sizeof(payload),
           "{\"name\":\"Display Reset Command Sequence\","
           "\"uniq_id\":\"%s_display_reset_sequence\","
           "\"cmd_t\":\"%s/cmd/reset_sequence\",\"pl_prs\":\"1\","
           "\"entity_category\":\"diagnostic\",\"dev\":{\"ids\":[\"%s\"]}}",
           node.c_str(), base.c_str(), node.c_str());
  g_mqtt.publish(reset_seq_config.c_str(), payload, true);

  const String reboot_config =
      g_cfg_discovery_prefix + "/button/" + node + "_display_reboot/config";
  snprintf(payload, sizeof(payload),
           "{\"name\":\"Display Reboot\","
           "\"uniq_id\":\"%s_display_reboot\","
           "\"cmd_t\":\"%s/cmd/reboot\",\"pl_prs\":\"1\","
           "\"entity_category\":\"diagnostic\",\"dev\":{\"ids\":[\"%s\"]}}",
           node.c_str(), base.c_str(), node.c_str());
  g_mqtt.publish(reboot_config.c_str(), payload, true);

  const String temp_config =
      g_cfg_discovery_prefix + "/sensor/" + node + "_indoor_temperature/config";
  snprintf(payload, sizeof(payload),
           "{\"name\":\"Indoor Temperature\",\"uniq_id\":\"%s_indoor_temperature\","
           "\"stat_t\":\"%s/state/current_temp_c\",\"unit_of_meas\":\"\xC2\xB0""C\","
           "\"dev_cla\":\"temperature\",\"stat_cla\":\"measurement\","
           "\"dev\":{\"ids\":[\"%s\"],\"name\":\"%s\","
           "\"mf\":\"rgregg\",\"mdl\":\"ESP32 Thermostat\"}}",
           node.c_str(), base.c_str(), node.c_str(),
           g_cfg_hostname.c_str());
  g_mqtt.publish(temp_config.c_str(), payload, true);

  const String hum_config =
      g_cfg_discovery_prefix + "/sensor/" + node + "_indoor_humidity/config";
  snprintf(payload, sizeof(payload),
           "{\"name\":\"Indoor Humidity\",\"uniq_id\":\"%s_indoor_humidity\","
           "\"stat_t\":\"%s/state/current_humidity\",\"unit_of_meas\":\"%%\","
           "\"dev_cla\":\"humidity\",\"stat_cla\":\"measurement\","
           "\"dev\":{\"ids\":[\"%s\"]}}",
           node.c_str(), base.c_str(), node.c_str());
  g_mqtt.publish(hum_config.c_str(), payload, true);

  // Re-publish announce so /devices reflects the current hostname
  {
    char announce_buf[256];
    snprintf(announce_buf, sizeof(announce_buf),
             "{\"role\":\"display\",\"firmware\":\"%s\",\"name\":\"%s\",\"ip\":\"%s\"}",
             THERMOSTAT_FIRMWARE_VERSION, g_cfg_hostname.c_str(),
             WiFi.localIP().toString().c_str());
    g_mqtt.publish(self_topic_for("announce").c_str(), announce_buf, true);
  }

  g_mqtt_discovery_sent = true;
}

void mqtt_on_message(char *topic, uint8_t *payload, unsigned int length) {
  if (topic == nullptr || payload == nullptr) return;

  xSemaphoreTake(g_api_mutex, portMAX_DELAY);

  char value[128];
  const size_t copy_len = (length < sizeof(value) - 1) ? length : sizeof(value) - 1;
  memcpy(value, payload, copy_len);
  value[copy_len] = '\0';
  if (length >= sizeof(value)) {
    Serial.printf("[mqtt] payload truncated: %u -> %u bytes topic=%s\n",
                  length, static_cast<unsigned>(sizeof(value) - 1), topic);
  }
  char normalized[128];
  memcpy(normalized, value, copy_len + 1);
  lower_in_place(normalized);

  const uint32_t now = millis();
  const String topic_str(topic);

  // Device discovery: parse announce topics from other devices
  // Topic pattern: {base}/devices/{mac}/announce
  {
    const String announce_prefix = g_cfg_base_topic + "/devices/";
    const String announce_suffix = "/announce";
    if (topic_str.startsWith(announce_prefix) && topic_str.endsWith(announce_suffix)) {
      int mac_begin = announce_prefix.length();
      int mac_end = topic_str.length() - announce_suffix.length();
      if (mac_end > mac_begin) {
        String peer_mac = topic_str.substring(mac_begin, mac_end);
        if (peer_mac != g_cfg_device_mac_compact) {
          char buf[256];
          size_t buf_len = (length < sizeof(buf) - 1) ? length : sizeof(buf) - 1;
          memcpy(buf, payload, buf_len);
          buf[buf_len] = '\0';
          char name[48] = "", role[16] = "", ip[16] = "";
          bool ok = ::json_extract_string(buf, "name", name, sizeof(name))
                  && ::json_extract_string(buf, "role", role, sizeof(role))
                  && ::json_extract_string(buf, "ip", ip, sizeof(ip));
          if (ok) {
            char formatted_mac[18];
            format_mac_colons(peer_mac.c_str(), formatted_mac, sizeof(formatted_mac));
            g_device_registry.upsert(formatted_mac, name, role, ip);
          }
        }
      }
      xSemaphoreGive(g_api_mutex);
      return;
    }
  }

  if (g_runtime == nullptr) {
    xSemaphoreGive(g_api_mutex);
    return;
  }
  if (topic_str.startsWith(self_topic_for("cmd/"))) {
    g_last_mqtt_command_ms = now;
  }

  if (topic_str == self_topic_for("cmd/mode")) {
    if (strcmp(normalized, "heat") == 0) {
      g_runtime->on_user_set_mode(FurnaceMode::Heat, now);
    } else if (strcmp(normalized, "cool") == 0) {
      g_runtime->on_user_set_mode(FurnaceMode::Cool, now);
    } else {
      g_runtime->on_user_set_mode(FurnaceMode::Off, now);
    }
  } else if (topic_str == self_topic_for("cmd/fan_mode")) {
    if (strcmp(normalized, "on") == 0 || strcmp(normalized, "always on") == 0) {
      g_runtime->on_user_set_fan_mode(FanMode::AlwaysOn, now);
    } else if (strcmp(normalized, "circulate") == 0) {
      g_runtime->on_user_set_fan_mode(FanMode::Circulate, now);
    } else {
      g_runtime->on_user_set_fan_mode(FanMode::Automatic, now);
    }
  } else if (topic_str == self_topic_for("cmd/target_temp_c")) {
    float celsius = static_cast<float>(atof(value));
    if (std::isfinite(celsius)) {
      if (celsius < 0.0f) celsius = 0.0f;
      if (celsius > 40.0f) celsius = 40.0f;
      g_runtime->on_user_set_setpoint_c(celsius, now);
    }
  } else if (topic_str == self_topic_for("cmd/unit")) {
    g_cfg_temp_unit_f = strcmp(normalized, "f") == 0 || strcmp(normalized, "fahrenheit") == 0;
    g_runtime->set_temperature_unit(g_cfg_temp_unit_f ? TemperatureUnit::Fahrenheit
                                                      : TemperatureUnit::Celsius);
    if (g_cfg_ready) {
      g_cfg.putBool("temp_u_f", g_cfg_temp_unit_f);
    }
  } else if (topic_str == self_topic_for("cmd/sync")) {
    if (parse_bool_payload(normalized)) {
      g_runtime->request_sync(now);
    }
  } else if (topic_str == self_topic_for("cmd/reboot")) {
    if (parse_bool_payload(normalized)) {
      schedule_reboot();
    }
  } else if (topic_str == self_topic_for("cmd/reset_sequence")) {
    if (parse_bool_payload(normalized)) {
      g_runtime->reset_local_command_sequence();
      g_runtime->request_sync(now);
    }
  } else if (topic_str == self_topic_for("cmd/filter_reset")) {
    if (parse_bool_payload(normalized)) {
      g_runtime->request_filter_reset(now);
    }
  } else if (topic_str == self_topic_for("cmd/temp_comp_c")) {
    float comp = static_cast<float>(atof(value));
    if (std::isfinite(comp)) {
      if (comp < -10.0f) comp = -10.0f;
      if (comp > 10.0f) comp = 10.0f;
      g_cfg_temp_comp_c = comp;
      g_runtime->set_local_temperature_compensation_c(g_cfg_temp_comp_c);
      g_last_sensor_poll_ms = 0;  // re-read sensor with new compensation
      if (g_cfg_ready) {
        g_cfg.putFloat("temp_comp", g_cfg_temp_comp_c);
      }
    }
  } else if (topic_str == self_topic_for("cmd/display_timeout_s")) {
    long seconds = atol(value);
    if (seconds < 30) seconds = 30;
    if (seconds > 600) seconds = 600;
    g_display_timeout_ms = static_cast<uint32_t>(seconds) * 1000UL;
    if (g_cfg_ready) {
      g_cfg.putUInt("disp_to_s", static_cast<uint32_t>(seconds));
    }
    g_screen.set_display_timeout_ms(g_display_timeout_ms);
  } else if (topic_str == self_topic_for("cmd/backlight_active_pct")) {
    g_cfg_backlight_active_pct = clamp_percent(atol(value));
    if (g_cfg_ready) {
      g_cfg.putUChar("bl_act", g_cfg_backlight_active_pct);
    }
  } else if (topic_str == self_topic_for("cmd/backlight_screensaver_pct")) {
    g_cfg_backlight_screensaver_pct = clamp_percent(atol(value));
    if (g_cfg_ready) {
      g_cfg.putUChar("bl_dim", g_cfg_backlight_screensaver_pct);
    }
  }

  // Controller state topics (MQTT-primary path)
  if (controller_mac_compact().length() > 0) {
    if (topic_str == controller_topic_for("state/mode")) {
      g_mqtt_ctrl_mode = mqtt_payload::str_to_mode(normalized);
      g_mqtt_ctrl_last_update_ms = now;
    } else if (topic_str == controller_topic_for("state/fan_mode")) {
      g_mqtt_ctrl_fan = mqtt_payload::str_to_fan(normalized);
      g_mqtt_ctrl_last_update_ms = now;
    } else if (topic_str == controller_topic_for("state/target_temp_c")) {
      float sp = static_cast<float>(atof(value));
      if (std::isfinite(sp)) {
        g_mqtt_ctrl_setpoint_c = sp;
        g_mqtt_ctrl_last_update_ms = now;
      }
    } else if (topic_str == controller_topic_for("state/furnace_state")) {
      g_mqtt_ctrl_state = mqtt_payload::str_to_furnace_state(value);
      g_mqtt_ctrl_last_update_ms = now;
    } else if (topic_str == controller_topic_for("state/lockout")) {
      g_mqtt_ctrl_lockout = mqtt_payload::parse_bool(value);
      g_mqtt_ctrl_last_update_ms = now;
    } else if (topic_str == controller_topic_for("state/windows_open")) {
      g_mqtt_ctrl_windows_open = mqtt_payload::parse_bool(value);
      g_mqtt_ctrl_last_update_ms = now;
    } else if (topic_str == controller_topic_for("state/filter_runtime_hours")) {
      float hours = static_cast<float>(atof(value));
      if (std::isfinite(hours) && hours >= 0.0f) {
        g_mqtt_ctrl_filter_runtime_s = static_cast<uint32_t>(hours * 3600.0f);
        g_mqtt_ctrl_last_update_ms = now;
      }
    } else if (topic_str == controller_topic_for("state/outdoor_temp_c")) {
      float temp = static_cast<float>(atof(value));
      if (std::isfinite(temp) && g_runtime != nullptr) {
        g_outdoor_temp_c = temp;
        g_runtime->on_outdoor_weather_update(g_outdoor_temp_c, g_weather_icon);
        g_have_weather_data = true;
      }
    } else if (topic_str == controller_topic_for("state/weather_condition")) {
      WeatherIcon icon = weather_icon_from_api(normalized);
      if (icon == WeatherIcon::Unknown) {
        // Try matching display text for conditions published as English names
        for (uint8_t i = 0; i <= static_cast<uint8_t>(WeatherIcon::Unknown); ++i) {
          const auto candidate = static_cast<WeatherIcon>(i);
          char lower_display[32];
          const char *display = weather_icon_display_text(candidate);
          size_t j = 0;
          for (; display[j] != '\0' && j < sizeof(lower_display) - 1; ++j) {
            lower_display[j] = static_cast<char>(
                std::tolower(static_cast<unsigned char>(display[j])));
          }
          lower_display[j] = '\0';
          if (strcmp(normalized, lower_display) == 0) {
            icon = candidate;
            break;
          }
        }
      }
      if (g_runtime != nullptr) {
        g_weather_icon = icon;
        g_runtime->on_outdoor_weather_update(g_outdoor_temp_c, g_weather_icon);
        g_have_weather_data = true;
      }
    } else if (topic_str == controller_topic_for("state/current_temp_c")) {
      float temp = static_cast<float>(atof(value));
      if (std::isfinite(temp)) {
        g_remote_indoor_temp_c = temp;
      }
    } else if (topic_str == controller_topic_for("state/current_humidity")) {
      float hum = static_cast<float>(atof(value));
      if (std::isfinite(hum)) {
        g_remote_indoor_humidity = hum;
      }
    } else if (topic_str == controller_topic_for("state/availability")) {
      g_mqtt_ctrl_available = strcmp(normalized, "online") == 0;
    }
  }

  mqtt_publish_state();
  xSemaphoreGive(g_api_mutex);
}

void wifi_event_handler(arduino_event_t *event) {
  if (event == nullptr) return;
  if (event->event_id == ARDUINO_EVENT_WIFI_STA_GOT_IP) {
    g_wifi.on_wifi_connected();
  }
}

void ensure_wifi_connected(uint32_t now_ms) {
  g_wifi.ensure_connected(now_ms);
}

void ensure_mqtt_connected(uint32_t now_ms) {
  if (g_cfg_mqtt_host.length() == 0 || !g_cfg_mqtt_enabled) return;
  if (WiFi.status() != WL_CONNECTED) return;
  if (g_cfg_mqtt_reconfigure_required) {
    g_cfg_mqtt_reconfigure_required = false;
    g_mqtt_discovery_sent = false;
    g_mqtt.disconnect();
  }
  if (g_mqtt.connected()) return;
  if ((now_ms - g_last_mqtt_attempt_ms) < kNetworkRetryMs) return;

  g_last_mqtt_attempt_ms = now_ms;
  g_mqtt.setServer(g_cfg_mqtt_host.c_str(), g_cfg_mqtt_port);

  bool ok = false;
  String will_topic = self_topic_for("state/availability");
  if (g_cfg_mqtt_user.length() == 0) {
    ok = g_mqtt.connect(g_cfg_mqtt_client_id.c_str(),
                        will_topic.c_str(), 1, true, "offline");
  } else {
    ok = g_mqtt.connect(g_cfg_mqtt_client_id.c_str(),
                        g_cfg_mqtt_user.c_str(), g_cfg_mqtt_password.c_str(),
                        will_topic.c_str(), 1, true, "offline");
  }

  if (!ok) {
    g_last_mqtt_error = String("connect_state_") + String(g_mqtt.state());
    return;
  }
  g_last_mqtt_error = "none";

  g_mqtt.subscribe(self_topic_for("cmd/mode").c_str());
  g_mqtt.subscribe(self_topic_for("cmd/fan_mode").c_str());
  g_mqtt.subscribe(self_topic_for("cmd/target_temp_c").c_str());
  g_mqtt.subscribe(self_topic_for("cmd/unit").c_str());
  g_mqtt.subscribe(self_topic_for("cmd/sync").c_str());
  g_mqtt.subscribe(self_topic_for("cmd/reboot").c_str());
  g_mqtt.subscribe(self_topic_for("cmd/reset_sequence").c_str());
  g_mqtt.subscribe(self_topic_for("cmd/filter_reset").c_str());
  g_mqtt.subscribe(self_topic_for("cmd/temp_comp_c").c_str());
  g_mqtt.subscribe(self_topic_for("cmd/display_timeout_s").c_str());
  g_mqtt.subscribe(self_topic_for("cmd/backlight_active_pct").c_str());
  g_mqtt.subscribe(self_topic_for("cmd/backlight_screensaver_pct").c_str());

  if (controller_mac_compact().length() > 0) {
    g_mqtt.subscribe(controller_topic_for("state/mode").c_str());
    g_mqtt.subscribe(controller_topic_for("state/fan_mode").c_str());
    g_mqtt.subscribe(controller_topic_for("state/target_temp_c").c_str());
    g_mqtt.subscribe(controller_topic_for("state/furnace_state").c_str());
    g_mqtt.subscribe(controller_topic_for("state/lockout").c_str());
    g_mqtt.subscribe(controller_topic_for("state/windows_open").c_str());
    g_mqtt.subscribe(controller_topic_for("state/filter_runtime_hours").c_str());
    g_mqtt.subscribe(controller_topic_for("state/outdoor_temp_c").c_str());
    g_mqtt.subscribe(controller_topic_for("state/weather_condition").c_str());
    g_mqtt.subscribe(controller_topic_for("state/availability").c_str());
    g_mqtt.subscribe(controller_topic_for("state/current_temp_c").c_str());
    g_mqtt.subscribe(controller_topic_for("state/current_humidity").c_str());
  }

  // Subscribe to device announce topics for discovery
  g_mqtt.subscribe(device_topic_for("+", "announce").c_str());

  if (g_cfg_ha_discovery_enabled) {
    mqtt_publish_discovery();
  }
  mqtt_publish_state();

  // Publish our announce message so other devices can discover us
  {
    char announce_buf[256];
    snprintf(announce_buf, sizeof(announce_buf),
             "{\"role\":\"display\",\"firmware\":\"%s\",\"name\":\"%s\",\"ip\":\"%s\"}",
             THERMOSTAT_FIRMWARE_VERSION, g_cfg_hostname.c_str(),
             WiFi.localIP().toString().c_str());
    g_mqtt.publish(self_topic_for("announce").c_str(), announce_buf, true);
  }
}

void ensure_mdns_ready() {
  if (WiFi.status() != WL_CONNECTED || g_mdns_started) return;
  const char *host =
      g_cfg_hostname.length() > 0 ? g_cfg_hostname.c_str() : "furnace-display";
  if (MDNS.begin(host)) {
    MDNS.addService("http", "tcp", 80);
    g_mdns_started = true;
  }
}

void rgb_flush_cb(lv_disp_drv_t *disp_drv, const lv_area_t *area, lv_color_t *color_p) {
  if (g_panel == nullptr || g_flush_ready_sem == nullptr) {
    lv_disp_flush_ready(disp_drv);
    return;
  }
  // Drain any stale VSYNC signals so the take below waits for the
  // VSYNC that happens *after* draw_bitmap queues the buffer swap.
  xSemaphoreTake(g_flush_ready_sem, 0);

  esp_lcd_rgb_panel_restart(g_panel);
  esp_lcd_panel_draw_bitmap(g_panel, 0, 0, kDisplayWidth, kDisplayHeight, color_p);

  // Wait for the buffer swap to actually complete at VSYNC before
  // letting LVGL draw into the next buffer.
  xSemaphoreTake(g_flush_ready_sem, pdMS_TO_TICKS(100));
  lv_disp_flush_ready(disp_drv);
}

bool gt911_read(uint16_t reg, uint8_t *buf, size_t len) {
  g_touch_i2c.beginTransmission(kGt911Addr);
  g_touch_i2c.write(static_cast<uint8_t>((reg >> 8) & 0xFF));
  g_touch_i2c.write(static_cast<uint8_t>(reg & 0xFF));
  if (g_touch_i2c.endTransmission(false) != 0) {
    return false;
  }

  const size_t read =
      g_touch_i2c.requestFrom(static_cast<int>(kGt911Addr), static_cast<int>(len));
  if (read != len) {
    return false;
  }

  for (size_t i = 0; i < len; ++i) {
    buf[i] = g_touch_i2c.read();
  }
  return true;
}

bool gt911_write(uint16_t reg, uint8_t val) {
  g_touch_i2c.beginTransmission(kGt911Addr);
  g_touch_i2c.write(static_cast<uint8_t>((reg >> 8) & 0xFF));
  g_touch_i2c.write(static_cast<uint8_t>(reg & 0xFF));
  g_touch_i2c.write(val);
  return g_touch_i2c.endTransmission() == 0;
}

void show_page(ThermostatPage page);
void apply_backlight(bool screensaver_active);

void poll_touch() {
  if (!g_sensors_initialized) { g_touch.touched = false; return; }
  uint8_t status = 0;
  if (!gt911_read(0x814E, &status, 1)) {
    g_touch.touched = false;
    return;
  }

  const uint8_t points = status & 0x0F;
  if ((status & 0x80) == 0 || points == 0) {
    g_touch.touched = false;
    gt911_write(0x814E, 0);
    return;
  }

  uint8_t data[8] = {0};
  if (!gt911_read(0x8150, data, sizeof(data))) {
    g_touch.touched = false;
    return;
  }

  const uint16_t raw_x = static_cast<uint16_t>(data[1] << 8 | data[0]);
  const uint16_t raw_y = static_cast<uint16_t>(data[3] << 8 | data[2]);

  // Scale touch coordinates to display resolution if GT911 config differs
  const int16_t x = (g_touch_x_max > 0 && g_touch_x_max != kDisplayWidth)
                        ? static_cast<int16_t>(static_cast<uint32_t>(raw_x) * kDisplayWidth / g_touch_x_max)
                        : static_cast<int16_t>(raw_x);
  const int16_t y = (g_touch_y_max > 0 && g_touch_y_max != kDisplayHeight)
                        ? static_cast<int16_t>(static_cast<uint32_t>(raw_y) * kDisplayHeight / g_touch_y_max)
                        : static_cast<int16_t>(raw_y);

  g_touch.touched = true;
  g_touch.x = x;
  g_touch.y = y;

  gt911_write(0x814E, 0);
}

void touch_read_cb(lv_indev_drv_t *, lv_indev_data_t *data) {
  poll_touch();
  if (g_touch.touched) {
    data->state = LV_INDEV_STATE_PRESSED;
    data->point.x = g_touch.x;
    data->point.y = g_touch.y;
    const bool was_screensaver = g_screen.screensaver_active();
    g_screen.on_user_interaction(millis());
    if (was_screensaver && !g_screen.screensaver_active()) {
      show_page(g_screen.current_page());
      apply_backlight(false);
    }
  } else {
    data->state = LV_INDEV_STATE_RELEASED;
  }
}

void show_page(ThermostatPage page) {
  if (g_home_page == nullptr) return;

  lv_obj_add_flag(g_home_page, LV_OBJ_FLAG_HIDDEN);
  lv_obj_add_flag(g_fan_page, LV_OBJ_FLAG_HIDDEN);
  lv_obj_add_flag(g_mode_page, LV_OBJ_FLAG_HIDDEN);
  lv_obj_add_flag(g_settings_page, LV_OBJ_FLAG_HIDDEN);
  lv_obj_add_flag(g_screensaver_page, LV_OBJ_FLAG_HIDDEN);

  switch (page) {
    case ThermostatPage::Home:
      lv_obj_clear_flag(g_home_page, LV_OBJ_FLAG_HIDDEN);
      break;
    case ThermostatPage::Fan:
      lv_obj_clear_flag(g_fan_page, LV_OBJ_FLAG_HIDDEN);
      break;
    case ThermostatPage::Mode:
      lv_obj_clear_flag(g_mode_page, LV_OBJ_FLAG_HIDDEN);
      break;
    case ThermostatPage::Settings:
      lv_obj_clear_flag(g_settings_page, LV_OBJ_FLAG_HIDDEN);
      break;
    case ThermostatPage::Screensaver:
      lv_obj_clear_flag(g_screensaver_page, LV_OBJ_FLAG_HIDDEN);
      break;
  }

  if (g_tabs != nullptr) {
    if (page == ThermostatPage::Screensaver) {
      lv_obj_add_flag(g_tabs, LV_OBJ_FLAG_HIDDEN);
    } else {
      lv_obj_clear_flag(g_tabs, LV_OBJ_FLAG_HIDDEN);
    }
  }
}

void apply_backlight(bool screensaver_active) {
  if (!g_backlight_enabled) {
    ledcWrite(kBacklightPin, 0);
    return;
  }
  const uint8_t duty =
      screensaver_active ? percent_to_duty(g_cfg_backlight_screensaver_pct)
                         : percent_to_duty(g_cfg_backlight_active_pct);
  ledcWrite(kBacklightPin, duty);
}

void refresh_ui() {
  if (g_runtime == nullptr || !g_ui_ready) return;

  const uint32_t now = millis();

  if (g_status_label != nullptr) lv_label_set_text(g_status_label, g_runtime->status_text(now).c_str());
  if (g_indoor_label != nullptr) lv_label_set_text(g_indoor_label, g_runtime->indoor_temp_text().c_str());
  if (g_humidity_label != nullptr) lv_label_set_text(g_humidity_label, g_runtime->indoor_humidity_text().c_str());
  if (g_setpoint_label != nullptr) lv_label_set_text(g_setpoint_label, g_runtime->setpoint_text().c_str());
  // Show/hide outdoor section based on weather data availability
  if (g_outdoor_section != nullptr) {
    if (g_have_weather_data) {
      lv_obj_clear_flag(g_outdoor_section, LV_OBJ_FLAG_HIDDEN);
      lv_label_set_text(g_weather_label, g_runtime->weather_text().c_str());
      if (g_weather_icon_label != nullptr) {
        lv_label_set_text(g_weather_icon_label,
                          thermostat::ui::weather_icon_symbol(g_runtime->weather_icon()));
      }
    } else {
      lv_obj_add_flag(g_outdoor_section, LV_OBJ_FLAG_HIDDEN);
    }
  }

  if (g_home_time_label != nullptr) {
    lv_label_set_text(g_home_time_label, current_time_text().c_str());
  }
  if (g_home_date_label != nullptr) {
    lv_label_set_text(g_home_date_label, current_date_text().c_str());
  }
  lv_label_set_text(g_screen_time_label, current_time_text().c_str());
  if (g_screen_weather_label != nullptr) {
    lv_label_set_text(g_screen_weather_label, g_have_weather_data ? g_runtime->weather_text().c_str() : "");
  }
  if (g_screen_indoor_label != nullptr) {
    lv_label_set_text(g_screen_indoor_label, g_runtime->indoor_temp_text().c_str());
  }
  if (g_screen_status_label != nullptr) {
    lv_label_set_text(g_screen_status_label, g_runtime->status_text(now).c_str());
  }
  if (g_screen.screensaver_active()) {
    thermostat::ui::update_screensaver_layout(g_screen_time_label, g_screen_weather_label,
                                              g_screen_indoor_label, g_screen_status_label,
                                              now / 60000UL);
  }
  const bool wifi_connected = WiFi.status() == WL_CONNECTED;
  const bool mqtt_connected = g_mqtt.connected();
  const uint32_t uptime_s = now / 1000UL;
  const uint32_t last_mqtt_ms = g_last_mqtt_command_ms;
  const uint32_t last_ctrl_hb_ms = g_runtime->last_controller_heartbeat_ms();
  const uint32_t since_mqtt_ms = last_mqtt_ms > 0 ? (now - last_mqtt_ms) : 0;
  const uint32_t since_ctrl_ms = last_ctrl_hb_ms > 0 ? (now - last_ctrl_hb_ms) : 0;

  static char system_text[256];
  snprintf(system_text, sizeof(system_text),
    "fw: %s\nboot_count: %lu\nreset: %s\nuptime_s: %lu\nfree_heap_b: %lu",
    THERMOSTAT_FIRMWARE_VERSION,
    (unsigned long)g_boot_count,
    g_reset_reason.c_str(),
    (unsigned long)uptime_s,
    (unsigned long)esp_get_free_heap_size());

  static char wifi_text[256];
  {
    char ip_buf[20] = "N/A";
    char ssid_buf[64] = "N/A";
    if (wifi_connected) {
      snprintf(ip_buf, sizeof(ip_buf), "%s", WiFi.localIP().toString().c_str());
      snprintf(ssid_buf, sizeof(ssid_buf), "%s", WiFi.SSID().c_str());
    }
    snprintf(wifi_text, sizeof(wifi_text),
      "connected: %s\nip: %s\nssid: %s\nmac: %s\nchannel: %d\nrssi_dbm: %d",
      wifi_connected ? "yes" : "no",
      ip_buf, ssid_buf,
      WiFi.macAddress().c_str(),
      wifi_connected ? WiFi.channel() : 0,
      wifi_connected ? (int)WiFi.RSSI() : 0);
  }

  static char mqtt_text[300];
  snprintf(mqtt_text, sizeof(mqtt_text),
    "connected: %s\nstate: %d\nhost: %s:%u\nclient_id: %s\nbase_topic: %s\nuser: %s\npassword: %s\nlast_cmd_ms: %lu\nsince_cmd_ms: %lu",
    mqtt_connected ? "yes" : "no",
    g_mqtt.state(),
    g_cfg_mqtt_host.c_str(),
    (unsigned)g_cfg_mqtt_port,
    g_cfg_mqtt_client_id.c_str(),
    g_cfg_base_topic.c_str(),
    g_cfg_mqtt_user.length() > 0 ? g_cfg_mqtt_user.c_str() : "(none)",
    g_cfg_mqtt_password.length() > 0 ? "set" : "unset",
    (unsigned long)last_mqtt_ms,
    (unsigned long)since_mqtt_ms);

  static char controller_text[128];
  snprintf(controller_text, sizeof(controller_text),
    "last_hb_ms: %lu\nsince_hb_ms: %lu",
    (unsigned long)last_ctrl_hb_ms,
    (unsigned long)since_ctrl_ms);

  static char espnow_text[180];
  snprintf(espnow_text, sizeof(espnow_text),
    "channel: %u\npeer_mac: %s\ntx_ok: %lu\ntx_fail: %lu",
    (unsigned)g_cfg_espnow_channel,
    g_cfg_espnow_peer_mac.c_str(),
    (unsigned long)g_runtime->espnow_send_ok_count(),
    (unsigned long)g_runtime->espnow_send_fail_count());

  static char config_text[220];
  snprintf(config_text, sizeof(config_text),
    "temp_unit: %s\ntemp_comp_c: %.2f\ndisplay_timeout_s: %lu\nbrightness_pct: %u\nsaver_pct: %u\nreboot_required: %s\nreboot_pending: %s",
    g_cfg_temp_unit_f ? "F" : "C",
    (double)g_cfg_temp_comp_c,
    (unsigned long)(g_display_timeout_ms / 1000UL),
    (unsigned)g_cfg_backlight_active_pct,
    (unsigned)g_cfg_backlight_screensaver_pct,
    g_cfg_reboot_required ? "true" : "false",
    g_reboot_requested ? "true" : "false");

  static char errors_text[160];
  snprintf(errors_text, sizeof(errors_text),
    "mqtt: %s\nota: %s\nespnow: %s\nsensor_fails: %u",
    g_last_mqtt_error.c_str(),
    g_last_ota_error.c_str(),
    g_last_espnow_error.c_str(),
    (unsigned)g_sensor_fail_count);

  if (g_settings_system_label != nullptr) lv_label_set_text(g_settings_system_label, system_text);
  if (g_settings_wifi_label != nullptr) lv_label_set_text(g_settings_wifi_label, wifi_text);
  if (g_settings_mqtt_label != nullptr) lv_label_set_text(g_settings_mqtt_label, mqtt_text);
  if (g_settings_controller_label != nullptr) {
    lv_label_set_text(g_settings_controller_label, controller_text);
  }
  if (g_settings_espnow_label != nullptr) lv_label_set_text(g_settings_espnow_label, espnow_text);
  if (g_settings_config_label != nullptr) lv_label_set_text(g_settings_config_label, config_text);
  if (g_settings_errors_label != nullptr) lv_label_set_text(g_settings_errors_label, errors_text);
  if (g_settings_display_label != nullptr) lv_label_set_text(g_settings_display_label, system_text);
  if (g_settings_diag_label != nullptr) lv_label_set_text(g_settings_diag_label, errors_text);
  if (g_timeout_slider != nullptr && !lv_obj_has_state(g_timeout_slider, LV_STATE_PRESSED)) {
    lv_slider_set_value(g_timeout_slider, static_cast<int32_t>(g_display_timeout_ms / 1000UL),
                        LV_ANIM_OFF);
  }
  if (g_brightness_slider != nullptr && !lv_obj_has_state(g_brightness_slider, LV_STATE_PRESSED)) {
    lv_slider_set_value(g_brightness_slider, static_cast<int32_t>(g_cfg_backlight_active_pct),
                        LV_ANIM_OFF);
  }
  if (g_dim_slider != nullptr && !lv_obj_has_state(g_dim_slider, LV_STATE_PRESSED)) {
    lv_slider_set_value(g_dim_slider, static_cast<int32_t>(g_cfg_backlight_screensaver_pct),
                        LV_ANIM_OFF);
  }

  // Controller connectivity check
  const uint32_t mqtt_cmd_ms = g_last_mqtt_command_ms;
  const uint32_t mqtt_ctrl_ms = g_mqtt_ctrl_last_update_ms;
  const uint32_t espnow_ms = g_runtime->last_controller_heartbeat_ms();
  const bool controller_connected =
      (mqtt_cmd_ms > 0 && (now - mqtt_cmd_ms) < g_cfg_controller_timeout_ms) ||
      (mqtt_ctrl_ms > 0 && (now - mqtt_ctrl_ms) < g_cfg_controller_timeout_ms) ||
      (espnow_ms > 0 && (now - espnow_ms) < g_cfg_controller_timeout_ms);

  thermostat::ui::set_mode_button_state(g_runtime->local_mode());
  thermostat::ui::set_fan_button_state(g_runtime->local_fan_mode());
  thermostat::ui::set_temperature_unit_button_state(g_runtime->temperature_unit());
  g_screen.on_mode_changed(g_runtime->local_mode());
  if (g_setpoint_column != nullptr) {
    if (controller_connected && g_screen.setpoint_visible()) {
      lv_obj_clear_flag(g_setpoint_column, LV_OBJ_FLAG_HIDDEN);
    } else {
      lv_obj_add_flag(g_setpoint_column, LV_OBJ_FLAG_HIDDEN);
    }
  }
  if (g_filter_label != nullptr) {
    if (g_runtime->filter_runtime_hours() >= kFilterChangeThresholdHours) {
      lv_label_set_text(g_filter_label, "Change Filter");
      lv_obj_clear_flag(g_filter_label, LV_OBJ_FLAG_HIDDEN);
    } else {
      lv_obj_add_flag(g_filter_label, LV_OBJ_FLAG_HIDDEN);
    }
  }

  // Fan page status + button state
  if (g_fan_status_label != nullptr) {
    if (!controller_connected) {
      lv_label_set_text(g_fan_status_label, "Not Connected");
    } else {
      const FurnaceStateCode cs = g_runtime->controller_state();
      const char *fan_text = (cs == FurnaceStateCode::HeatOn || cs == FurnaceStateCode::CoolOn ||
                              cs == FurnaceStateCode::FanOn)
                                 ? "Fan Running"
                                 : "Idle";
      lv_label_set_text(g_fan_status_label, fan_text);
    }
  }
  thermostat::ui::set_fan_mode_buttons_enabled(controller_connected);

  // Mode page status + button state
  if (g_mode_status_label != nullptr) {
    if (!controller_connected) {
      lv_label_set_text(g_mode_status_label, "Not Connected");
    } else {
      lv_label_set_text(g_mode_status_label, g_runtime->status_text(now).c_str());
    }
  }
  thermostat::ui::set_mode_buttons_enabled(controller_connected);
}

void tab_event_cb(lv_event_t *) {
  if (g_runtime == nullptr) return;
  const char *txt = lv_btnmatrix_get_btn_text(g_tabs, lv_btnmatrix_get_selected_btn(g_tabs));
  const uint32_t now = millis();
  if (strcmp(txt, "HOME") == 0) {
    g_screen.on_tab_selected(ThermostatPage::Home, now);
  } else if (strcmp(txt, "FAN") == 0) {
    g_screen.on_tab_selected(ThermostatPage::Fan, now);
  } else if (strcmp(txt, "MODE") == 0) {
    g_screen.on_tab_selected(ThermostatPage::Mode, now);
  } else if (strcmp(txt, "SETTINGS") == 0) {
    g_screen.on_tab_selected(ThermostatPage::Settings, now);
  }
  show_page(g_screen.current_page());
}

void btn_setpoint_up_cb(lv_event_t *) {
  if (g_runtime == nullptr) return;
  const float step = (g_runtime->temperature_unit() == TemperatureUnit::Fahrenheit) ? 1.0f : 0.5f;
  const float user_val = g_runtime->temperature_unit() == TemperatureUnit::Fahrenheit
                             ? ((g_runtime->local_setpoint_c() * 9.0f / 5.0f) + 32.0f)
                             : g_runtime->local_setpoint_c();
  g_runtime->on_user_set_setpoint(user_val + step, millis());
}

void btn_setpoint_down_cb(lv_event_t *) {
  if (g_runtime == nullptr) return;
  const float step = (g_runtime->temperature_unit() == TemperatureUnit::Fahrenheit) ? 1.0f : 0.5f;
  const float user_val = g_runtime->temperature_unit() == TemperatureUnit::Fahrenheit
                             ? ((g_runtime->local_setpoint_c() * 9.0f / 5.0f) + 32.0f)
                             : g_runtime->local_setpoint_c();
  g_runtime->on_user_set_setpoint(user_val - step, millis());
}

void btn_mode_cb(lv_event_t *e) {
  if (g_runtime == nullptr) return;
  auto mode = static_cast<FurnaceMode>(reinterpret_cast<uintptr_t>(lv_event_get_user_data(e)));
  g_runtime->on_user_set_mode(mode, millis());
}

void btn_fan_cb(lv_event_t *e) {
  if (g_runtime == nullptr) return;
  auto mode = static_cast<FanMode>(reinterpret_cast<uintptr_t>(lv_event_get_user_data(e)));
  g_runtime->on_user_set_fan_mode(mode, millis());
}

void btn_unit_cb(lv_event_t *e) {
  auto unit = static_cast<TemperatureUnit>(reinterpret_cast<uintptr_t>(lv_event_get_user_data(e)));
  const char *raw = (unit == TemperatureUnit::Fahrenheit) ? "f" : "c";
  try_update_runtime_config("temperature_unit", raw);
  mqtt_publish_state();
}

void btn_sync_cb(lv_event_t *) {
  if (g_runtime == nullptr) return;
  g_runtime->request_sync(millis());
}

void btn_filter_reset_cb(lv_event_t *) {
  if (g_runtime == nullptr) return;
  g_runtime->request_filter_reset(millis());
}

void apply_runtime_u32_setting(const char *key, uint32_t value) {
  String raw(value);
  if (try_update_runtime_config(key, raw.c_str())) {
    mqtt_publish_state();
  }
}

uint32_t snap_to_step(uint32_t value, uint32_t step, uint32_t min_v, uint32_t max_v) {
  if (value < min_v) value = min_v;
  if (value > max_v) value = max_v;
  const uint32_t snapped = ((value + (step / 2U)) / step) * step;
  if (snapped < min_v) return min_v;
  if (snapped > max_v) return max_v;
  return snapped;
}

void timeout_slider_cb(lv_event_t *e) {
  lv_obj_t *slider = lv_event_get_target(e);
  if (slider == nullptr) return;
  uint32_t seconds = static_cast<uint32_t>(lv_slider_get_value(slider));
  seconds = snap_to_step(seconds, 30U, 30U, 600U);
  lv_slider_set_value(slider, static_cast<int32_t>(seconds), LV_ANIM_OFF);
  apply_runtime_u32_setting("display_timeout_s", seconds);
}

void brightness_slider_cb(lv_event_t *e) {
  lv_obj_t *slider = lv_event_get_target(e);
  if (slider == nullptr) return;
  uint32_t percent = static_cast<uint32_t>(lv_slider_get_value(slider));
  percent = snap_to_step(percent, 5U, 0U, 100U);
  lv_slider_set_value(slider, static_cast<int32_t>(percent), LV_ANIM_OFF);
  apply_runtime_u32_setting("backlight_active_pct", percent);
}

void dim_slider_cb(lv_event_t *e) {
  lv_obj_t *slider = lv_event_get_target(e);
  if (slider == nullptr) return;
  uint32_t percent = static_cast<uint32_t>(lv_slider_get_value(slider));
  percent = snap_to_step(percent, 5U, 0U, 100U);
  lv_slider_set_value(slider, static_cast<int32_t>(percent), LV_ANIM_OFF);
  apply_runtime_u32_setting("backlight_screensaver_pct", percent);
}

void create_ui() {
  thermostat::ui::UiCallbacks callbacks{};
  callbacks.on_tab_changed = tab_event_cb;
  callbacks.on_setpoint_up = btn_setpoint_up_cb;
  callbacks.on_setpoint_down = btn_setpoint_down_cb;
  callbacks.on_mode = btn_mode_cb;
  callbacks.on_fan = btn_fan_cb;
  callbacks.on_unit = btn_unit_cb;
  callbacks.on_sync = btn_sync_cb;
  callbacks.on_filter_reset = btn_filter_reset_cb;
  callbacks.on_wifi_reset = [](lv_event_t *) {
    Serial.println("[ui] WiFi reset requested — clearing credentials and rebooting");
    g_wifi.clear_credentials();
    schedule_reboot();
  };
  callbacks.on_restart = [](lv_event_t *) {
    Serial.println("[ui] Restart requested");
    schedule_reboot();
  };
  callbacks.on_timeout_slider = timeout_slider_cb;
  callbacks.on_brightness_slider = brightness_slider_cb;
  callbacks.on_dim_slider = dim_slider_cb;

  thermostat::ui::UiHandles handles{};
  thermostat::ui::build_thermostat_ui(callbacks, &handles);

  g_tabs = handles.tabs;
  g_home_page = handles.home_page;
  g_fan_page = handles.fan_page;
  g_mode_page = handles.mode_page;
  g_settings_page = handles.settings_page;
  g_screensaver_page = handles.screensaver_page;
  g_status_label = handles.status_label;
  g_indoor_label = handles.indoor_label;
  g_humidity_label = handles.humidity_label;
  g_setpoint_label = handles.setpoint_label;
  g_outdoor_section = handles.outdoor_section;
  g_weather_label = handles.weather_label;
  g_weather_icon_label = handles.weather_icon_label;
  g_home_time_label = handles.home_time_label;
  g_home_date_label = handles.home_date_label;
  g_screen_time_label = handles.screen_time_label;
  g_screen_weather_label = handles.screen_weather_label;
  g_screen_indoor_label = handles.screen_indoor_label;
  g_screen_status_label = handles.screen_status_label;
  g_settings_diag_label = handles.settings_diag_label;
  g_settings_display_label = handles.settings_display_label;
  g_settings_system_label = handles.settings_system_label;
  g_settings_wifi_label = handles.settings_wifi_label;
  g_settings_mqtt_label = handles.settings_mqtt_label;
  g_settings_controller_label = handles.settings_controller_label;
  g_settings_espnow_label = handles.settings_espnow_label;
  g_settings_config_label = handles.settings_config_label;
  g_settings_errors_label = handles.settings_errors_label;
  g_timeout_slider = handles.timeout_slider;
  g_brightness_slider = handles.brightness_slider;
  g_dim_slider = handles.dim_slider;
  g_setpoint_column = handles.setpoint_column;
  g_filter_label = handles.filter_label;
  g_fan_status_label = handles.fan_status_label;
  g_mode_status_label = handles.mode_status_label;

  show_page(ThermostatPage::Home);
  g_ui_ready = true;
}

bool init_display_and_lvgl() {
  esp_lcd_rgb_panel_config_t panel_config = {};
  panel_config.clk_src = LCD_CLK_SRC_DEFAULT;
  panel_config.timings.pclk_hz = 14000000;
  panel_config.timings.h_res = kDisplayWidth;
  panel_config.timings.v_res = kDisplayHeight;
  panel_config.timings.hsync_back_porch = 8;
  panel_config.timings.hsync_front_porch = 8;
  panel_config.timings.hsync_pulse_width = 4;
  panel_config.timings.vsync_back_porch = 8;
  panel_config.timings.vsync_front_porch = 8;
  panel_config.timings.vsync_pulse_width = 4;
  panel_config.timings.flags.pclk_active_neg = 1;

  panel_config.data_width = 16;
  panel_config.de_gpio_num = 40;
  panel_config.pclk_gpio_num = 42;
  panel_config.vsync_gpio_num = 41;
  panel_config.hsync_gpio_num = 39;
  panel_config.disp_gpio_num = -1;

  // Pin order: R0-R4, G0-G5, B0-B4 (panel uses BGR element order)
  int pins[16] = {8, 3, 46, 9, 1, 5, 6, 7, 15, 16, 4, 45, 48, 47, 21, 14};
  for (size_t i = 0; i < 16; ++i) {
    panel_config.data_gpio_nums[i] = pins[i];
  }

  panel_config.flags.fb_in_psram = 1;
  // Bounce buffer is internal DMA-capable RAM (stages PSRAM framebuffer lines). 4
  // lines (~12.8 KB across the two ping-pong buffers) instead of 10 (~32 KB) keeps the
  // *contiguous* internal block modest — plenty for a low-refresh thermostat UI. (The
  // old NimBLE provisioning could fragment this region; provisioning is now SoftAP, but
  // the smaller buffer is kept as cheap headroom.)
  panel_config.bounce_buffer_size_px = 4 * kDisplayWidth;
  panel_config.num_fbs = 2;

  lv_init();

  delay(kDisplayInitSettleMs);
  if (esp_lcd_new_rgb_panel(&panel_config, &g_panel) != ESP_OK) {
    // Most common cause: not enough *contiguous* internal DMA RAM for the bounce
    // buffer (e.g. NimBLE fragmented it during provisioning boot). Don't register
    // an LVGL display with null buffers — that derefs a null default display and
    // panics. Run headless instead so the rest of the firmware stays up.
    Serial.println("[display] FATAL: esp_lcd_new_rgb_panel failed — running headless");
    g_panel = nullptr;
    g_display_ready = false;
    return false;
  }

  esp_lcd_panel_reset(g_panel);
  esp_lcd_panel_init(g_panel);

  // Register VSYNC callback so the flush can wait for the buffer swap
  g_flush_ready_sem = xSemaphoreCreateBinary();
  if (!g_flush_ready_sem) {
    Serial.println("[display] FATAL: failed to create VSYNC semaphore — running headless");
    // Release the panel's PSRAM framebuffers + contiguous internal bounce buffers
    // and null g_panel so the post-condition holds: g_display_ready == false implies
    // g_panel == nullptr. The reboot/OTA teardown paths gate on g_panel != nullptr,
    // so leaving a half-wired panel here would let them poke uninitialized hardware.
    esp_lcd_panel_del(g_panel);
    g_panel = nullptr;
    g_display_ready = false;
    return false;
  }
  esp_lcd_rgb_panel_event_callbacks_t cbs = {};
  cbs.on_vsync = on_vsync_ready;
  esp_lcd_rgb_panel_register_event_callbacks(g_panel, &cbs, nullptr);

  // Get the panel's two PSRAM framebuffers for double-buffered direct mode.
  // LVGL draws dirty areas into one buffer while the panel DMA reads the other.
  // On flush, esp_lcd_panel_draw_bitmap detects the source is a panel buffer
  // and does an atomic pointer swap instead of a copy.
  void *panel_fb0 = nullptr;
  void *panel_fb1 = nullptr;
  esp_lcd_rgb_panel_get_frame_buffer(g_panel, 2, &panel_fb0, &panel_fb1);

  const size_t buf_pixels = kDisplayWidth * kDisplayHeight;
  g_buf_1 = static_cast<lv_color_t *>(panel_fb0);
  g_buf_2 = static_cast<lv_color_t *>(panel_fb1);

  lv_disp_draw_buf_init(&g_draw_buf, g_buf_1, g_buf_2, buf_pixels);
  lv_disp_drv_init(&g_disp_drv);
  g_disp_drv.hor_res = kDisplayWidth;
  g_disp_drv.ver_res = kDisplayHeight;
  g_disp_drv.flush_cb = rgb_flush_cb;
  g_disp_drv.draw_buf = &g_draw_buf;
  g_disp_drv.direct_mode = 1;
  g_disp_drv.full_refresh = 1;
  lv_disp_drv_register(&g_disp_drv);

  // Touch input is only meaningful with a live display.
  lv_indev_drv_init(&g_indev_drv);
  g_indev_drv.type = LV_INDEV_TYPE_POINTER;
  g_indev_drv.read_cb = touch_read_cb;
  lv_indev_drv_register(&g_indev_drv);

  g_display_ready = true;
  return true;
}

void init_backlight() {
  ledcAttach(kBacklightPin, kBacklightFreq, kBacklightResolution);
  ledcWrite(kBacklightPin, 0);
  g_backlight_enabled = false;
  g_backlight_enable_at_ms = 0;
}

void init_sensors() {
  g_touch_i2c.begin(kTouchI2cSda, kTouchI2cScl, 400000U);
  g_sensor_i2c.begin(kSensorI2cSda, kSensorI2cScl, 100000U);

  // Try AHT20 first (I2C addr 0x38)
  if (g_aht.begin(&g_sensor_i2c)) {
    // Validate with a test read — ghost devices return 0.0/0.0
    sensors_event_t h, t;
    if (g_aht.getEvent(&h, &t) &&
        !(t.temperature == 0.0f && h.relative_humidity == 0.0f)) {
      g_sensor_type = SensorType::AHT;
      Serial.println("[sensor] AHT detected");
    }
  }
  // Try Si7021 if AHT not found (I2C addr 0x40)
  if (g_sensor_type == SensorType::None && g_si7021.begin()) {
    g_sensor_type = SensorType::Si7021;
    Serial.println("[sensor] Si7021 detected");
  }
  if (g_sensor_type == SensorType::None) {
    Serial.println("[sensor] no sensor detected");
  }

  // Read GT911 configured resolution for coordinate scaling
  uint8_t res[4] = {0};
  if (gt911_read(0x8048, res, 4)) {
    const uint16_t x_max = static_cast<uint16_t>(res[1] << 8 | res[0]);
    const uint16_t y_max = static_cast<uint16_t>(res[3] << 8 | res[2]);
    if (x_max > 0) g_touch_x_max = x_max;
    if (y_max > 0) g_touch_y_max = y_max;
    Serial.printf("[touch] GT911 resolution: %ux%u\n", g_touch_x_max, g_touch_y_max);
  }
  g_sensors_initialized = true;
}

void init_network() {
  // Read MAC address without starting the WiFi radio — keeps internal RAM
  // free for BLE provisioning on fresh devices with no stored SSID.
  {
    uint8_t mac[6];
    esp_read_mac(mac, ESP_MAC_WIFI_STA);
    char buf[18];
    snprintf(buf, sizeof(buf), "%02X:%02X:%02X:%02X:%02X:%02X", mac[0], mac[1], mac[2], mac[3], mac[4], mac[5]);
    g_cfg_device_mac = String(buf);
    g_cfg_device_mac_compact = mac_strip_colons(g_cfg_device_mac);
  }

  // Compute derived client ID from base_topic + device MAC
  {
    char cid_buf[64];
    mqtt_topics::client_id(cid_buf, sizeof(cid_buf), g_cfg_base_topic.c_str(), g_cfg_device_mac_compact.c_str());
    g_cfg_mqtt_client_id = String(cid_buf);
  }

  // Initialize WiFi provisioning manager
  WifiProvisioningConfig wifi_cfg = {};
  wifi_cfg.device_name = "Thermostat";
  wifi_cfg.firmware_name = THERMOSTAT_PROJECT_NAME;
  wifi_cfg.firmware_version = THERMOSTAT_FIRMWARE_VERSION;
  wifi_cfg.hardware_variant = "ESP32-S3";
  wifi_cfg.nvs = &g_cfg;
  // Baked creds (THERMOSTAT_WIFI_SSID/PASSWORD) seed the connection when NVS has none,
  // so a creds-baked build (e.g. the isolated bench) connects without provisioning.
  wifi_cfg.default_ssid = g_cfg_wifi_ssid.c_str();
  wifi_cfg.default_password = g_cfg_wifi_password.c_str();
  wifi_cfg.hostname = g_cfg_hostname.c_str();
  wifi_cfg.retry_interval_ms = kNetworkRetryMs;
  g_wifi.begin(wifi_cfg);
  WiFi.onEvent(wifi_event_handler);

  g_mqtt.setBufferSize(1024);
  g_mqtt.setServer(g_cfg_mqtt_host.c_str(), g_cfg_mqtt_port);
  g_mqtt.setCallback(mqtt_on_message);
  configTzTime(THERMOSTAT_TIME_TZ, THERMOSTAT_TIME_NTP_1, THERMOSTAT_TIME_NTP_2,
               THERMOSTAT_TIME_NTP_3);
}

void poll_sensors(uint32_t now_ms) {
  if (g_runtime == nullptr) return;
  if ((now_ms - g_last_sensor_poll_ms) < kSensorPollMs) return;

  g_last_sensor_poll_ms = now_ms;

  if (g_sensor_type == SensorType::AHT) {
    sensors_event_t humidity, temp;
    if (g_aht.getEvent(&humidity, &temp)) {
      g_sensor_fail_count = 0;
      g_runtime->on_local_sensor_update(temp.temperature, humidity.relative_humidity);
    } else {
      ++g_sensor_fail_count;
      Serial.printf("[sensor] AHT read failed (fail_count=%u)\n", (unsigned)g_sensor_fail_count);
      if (g_sensor_fail_count >= 5) {
        Serial.println("[sensor] too many failures, attempting I2C reset");
        g_sensor_i2c.end();
        g_sensor_i2c.begin(kSensorI2cSda, kSensorI2cScl, 100000U);
        g_sensor_type = SensorType::None;
        g_sensor_fail_count = 0;
        if (g_aht.begin(&g_sensor_i2c)) {
          sensors_event_t h, t;
          if (g_aht.getEvent(&h, &t) &&
              !(t.temperature == 0.0f && h.relative_humidity == 0.0f)) {
            g_sensor_type = SensorType::AHT;
            Serial.println("[sensor] AHT re-detected after reset");
          }
        }
        if (g_sensor_type == SensorType::None && g_si7021.begin()) {
          g_sensor_type = SensorType::Si7021;
          Serial.println("[sensor] Si7021 re-detected after reset");
        }
      }
    }
  } else if (g_sensor_type == SensorType::Si7021) {
    float temp = g_si7021.readTemperature();
    float hum = g_si7021.readHumidity();
    if (std::isfinite(temp) && std::isfinite(hum)) {
      g_sensor_fail_count = 0;
      g_runtime->on_local_sensor_update(temp, hum);
    } else {
      ++g_sensor_fail_count;
      Serial.printf("[sensor] Si7021 read failed (fail_count=%u)\n", (unsigned)g_sensor_fail_count);
      if (g_sensor_fail_count >= 5) {
        Serial.println("[sensor] too many failures, attempting I2C reset");
        g_sensor_i2c.end();
        g_sensor_i2c.begin(kSensorI2cSda, kSensorI2cScl, 100000U);
        g_sensor_type = SensorType::None;
        g_sensor_fail_count = 0;
        if (g_si7021.begin()) {
          g_sensor_type = SensorType::Si7021;
          Serial.println("[sensor] Si7021 re-detected after reset");
        } else if (g_aht.begin(&g_sensor_i2c)) {
          sensors_event_t h, t;
          if (g_aht.getEvent(&h, &t) &&
              !(t.temperature == 0.0f && h.relative_humidity == 0.0f)) {
            g_sensor_type = SensorType::AHT;
            Serial.println("[sensor] AHT re-detected after reset");
          }
        }
      }
    }
  } else if (!std::isnan(g_remote_indoor_temp_c)) {
    g_runtime->on_local_sensor_update(g_remote_indoor_temp_c, g_remote_indoor_humidity);
  }
  if (g_have_weather_data) {
    g_runtime->on_outdoor_weather_update(g_outdoor_temp_c, g_weather_icon);
  }
}

}  // namespace

// ---------- SoftAP provisioning boot mode ----------
// When no WiFi SSID is configured, we enter a minimal boot mode:
// 1. Init the LCD + bring up the SoftAP captive portal (no Bluetooth, so no internal-RAM
//    contention with the LCD framebuffers)
// 2. Show the AP name to join on the LCD (or run headless if the LCD failed)
// 3. Loop servicing the portal (DNS + web) until the user submits credentials → reboot
static bool g_provisioning_boot_mode = false;

extern "C" const lv_font_t thermostat_font_montserrat_20;
extern "C" const lv_font_t thermostat_font_montserrat_30;

static void run_provisioning_boot() {
  Serial.println("[provision] No WiFi configured — entering SoftAP portal mode");
  g_provisioning_boot_mode = true;

  // SoftAP provisioning uses only the WiFi stack (no Bluetooth), so the LCD comes up
  // cleanly with no internal-DMA-RAM contention.
  init_backlight();
  const bool disp_ok = init_display_and_lvgl();

  WifiProvisioningConfig wifi_cfg = {};
  wifi_cfg.device_name = "Thermostat";
  wifi_cfg.firmware_name = THERMOSTAT_PROJECT_NAME;
  wifi_cfg.firmware_version = THERMOSTAT_FIRMWARE_VERSION;
  wifi_cfg.hardware_variant = "ESP32-S3";
  wifi_cfg.nvs = &g_cfg;
  wifi_cfg.retry_interval_ms = kNetworkRetryMs;
  g_wifi.begin(wifi_cfg);
  g_wifi.start_provisioning();
  const String ap_ssid = softap_provisioning_ap_ssid();

  if (disp_ok) {
    // Provisioning screen: dark background, AP name to join.
    lv_obj_t *scr = lv_scr_act();
    lv_obj_set_style_bg_color(scr, lv_color_black(), 0);

    lv_obj_t *title = lv_label_create(scr);
    lv_label_set_text(title, "WiFi Setup");
    lv_obj_set_style_text_color(title, lv_color_white(), 0);
    lv_obj_set_style_text_font(title, &thermostat_font_montserrat_30, 0);
    lv_obj_align(title, LV_ALIGN_CENTER, 0, -50);

    lv_obj_t *body = lv_label_create(scr);
    const String msg =
        String("Join Wi-Fi network:\n") + ap_ssid + "\nthen open any web page";
    lv_label_set_text(body, msg.c_str());
    lv_obj_set_style_text_color(body, lv_color_make(0xCC, 0xCC, 0xCC), 0);
    lv_obj_set_style_text_font(body, &thermostat_font_montserrat_20, 0);
    lv_obj_set_style_text_align(body, LV_TEXT_ALIGN_CENTER, 0);
    lv_obj_align(body, LV_ALIGN_CENTER, 0, 20);

    ledcWrite(kBacklightPin, 200);
  } else {
    Serial.printf("[provision] Display unavailable — portal AP: %s\n", ap_ssid.c_str());
  }

  // Service the SoftAP portal until the user submits credentials, then reboot into
  // normal mode (which reads the new NVS creds and connects).
  esp_task_wdt_add(NULL);
  uint32_t last_tick = millis();
  for (;;) {
    esp_task_wdt_reset();
    const uint32_t now = millis();
    if (g_wifi.has_credentials()) {
      Serial.println("[provision] Credentials received — rebooting");
      delay(800);  // let the portal's "Saved" response flush to the browser
      ESP.restart();
    }
    g_wifi.ensure_connected(now);  // runs the DNS + portal web server
    if (disp_ok && (now - last_tick) >= kUiTickMs) {
      lv_tick_inc(now - last_tick);
      last_tick = now;
      lv_timer_handler();
    }
    delay(1);
  }
}

void thermostat_firmware_setup() {
  g_api_mutex = xSemaphoreCreateMutex();
  if (g_api_mutex == nullptr) {
    Serial.println("[init] FATAL: failed to create api_mutex");
    delay(3000);
    ESP.restart();
  }
  g_cfg_ready = g_cfg.begin("cfg_disp", false);
  load_runtime_config();
  g_boot_count = g_cfg_ready ? (g_cfg.getUInt("boot_cnt", 0U) + 1U) : 0U;
  if (g_cfg_ready) {
    g_cfg.putUInt("boot_cnt", g_boot_count);
  }
  g_reset_reason = reset_reason_text(esp_reset_reason());

  // If no WiFi SSID is configured, enter minimal BLE provisioning mode.
  // This must happen before display init to keep internal RAM free for BLE.
  // ESP-NOW-only mode skips this entirely — no SSID is needed and we must not
  // start BLE (it would fragment the internal RAM the LCD bounce buffer needs).
  if (!g_cfg_wifi_disabled && g_cfg_wifi_ssid.isEmpty()) {
    run_provisioning_boot();
    return;  // never reached — run_provisioning_boot loops forever
  }
  if (g_cfg_wifi_disabled) {
    Serial.println("[net] ESP-NOW-only mode — WiFi/MQTT/web disabled, ESP-NOW + LCD only");
    // No NTP in this mode; wall-clock time arrives over ESP-NOW from the controller.
    // Still set the timezone so the received UTC epoch renders as local time.
    setenv("TZ", THERMOSTAT_TIME_TZ, 1);
    tzset();
  }

  ThermostatDeviceRuntimeConfig cfg;
  static const uint8_t kBroadcast[6] = {0xFF, 0xFF, 0xFF, 0xFF, 0xFF, 0xFF};
  memcpy(cfg.transport.peer_mac, kBroadcast, sizeof(kBroadcast));
  cfg.transport.channel = g_cfg_espnow_channel;
  cfg.transport.heartbeat_interval_ms = 10000;
  cfg.controller_connection_timeout_ms = g_cfg_controller_timeout_ms;
  // Resync telemetry seq on reconnect after the same gap that marks "disconnected".
  cfg.app.controller_reconnect_resync_ms = g_cfg_controller_timeout_ms;
  if (g_cfg_espnow_enabled) {
    parse_mac(g_cfg_espnow_peer_mac.c_str(), cfg.transport.peer_mac);
    uint8_t lmk[16] = {0};
    if (parse_lmk_hex(g_cfg_espnow_lmk.c_str(), lmk) &&
        !is_broadcast_mac(cfg.transport.peer_mac)) {
      memcpy(cfg.transport.lmk, lmk, sizeof(lmk));
      cfg.transport.encrypted = true;
    }
  }

  static ThermostatDeviceRuntime runtime(cfg);
  g_runtime = &runtime;

  g_screen.set_display_timeout_ms(g_display_timeout_ms);
  g_screen.on_boot(millis());

  init_backlight();
  init_sensors();
  if (!g_cfg_wifi_disabled) {
    init_network();
  }
  if (init_display_and_lvgl()) {
    create_ui();
  } else {
    Serial.println("[display] Continuing headless — UI disabled; ESP-NOW/MQTT/sensors/web active");
  }
  g_backlight_enable_at_ms = millis() + kBacklightEnableDelayMs;

  bool runtime_ok = false;
  if (g_cfg_espnow_enabled) {
    runtime_ok = g_runtime->begin();
  }
  g_last_espnow_error = runtime_ok ? "none" : (g_cfg_espnow_enabled ? "begin_failed" : "disabled");
  g_runtime->set_local_temperature_compensation_c(g_cfg_temp_comp_c);
  g_runtime->set_temperature_unit(g_cfg_temp_unit_f ? TemperatureUnit::Fahrenheit
                                                    : TemperatureUnit::Celsius);
  ota_rollback_begin();

  // Web server task on Core 0 (alongside WiFi/BT stack): handles all HTTP
  // requests without blocking the LVGL/sensor/MQTT main loop on Core 1.
  // Create web task on Core 0 with stack in PSRAM to avoid consuming
  // internal SRAM that the WiFi driver needs for connection buffers.
  // Skipped in ESP-NOW-only mode — there is no IP for it to serve on.
  if (!g_cfg_wifi_disabled) {
    static StaticTask_t web_task_tcb;
    static StackType_t *web_task_stack = (StackType_t *)heap_caps_malloc(
        8192 * sizeof(StackType_t), MALLOC_CAP_SPIRAM);
    if (!web_task_stack) {
      Serial.println("[web] PSRAM alloc failed, falling back to internal SRAM");
      web_task_stack = (StackType_t *)heap_caps_malloc(
          8192 * sizeof(StackType_t), MALLOC_CAP_INTERNAL);
    }
    if (web_task_stack) {
      xTaskCreateStaticPinnedToCore(web_server_task, "web", 8192,
                                    nullptr, 1, web_task_stack, &web_task_tcb, 0);
    } else {
      Serial.println("[web] FATAL: failed to allocate web task stack");
    }
  }
  esp_task_wdt_add(NULL);  // register main task with TWDT
  // Raise the Task Watchdog timeout to 15s so a bounded MQTT-connect spin (see
  // setSocketTimeout below) can't starve the main task's esp_task_wdt_reset().
  // idle_core_mask=0: the display's explicit main+web task registration remains
  // the watchdog coverage (esp_task_wdt_add calls are unaffected by reconfigure).
  {
    esp_task_wdt_config_t wdt_cfg = {
        .timeout_ms = 15000,
        .idle_core_mask = 0,
        .trigger_panic = true,
    };
    esp_task_wdt_reconfigure(&wdt_cfg);
  }
  // Bound PubSubClient's connect/read busy-wait (PubSubClient.cpp:257 spins with
  // no yield for up to socketTimeout) to 5s, well under the 15s watchdog.
  g_mqtt.setSocketTimeout(5);
}
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
