rgregg/esp32-wireless-thermostat/include/controller/relay_backend.h

#pragma once

#include "thermostat_types.h"  // RelayDemand

namespace thermostat {

// Hardware seam for relay output. ControllerRelayIo owns the interlock logic and
// calls a backend to actually drive the relays. Implementations: GpioRelayBackend
// (direct GPIO), Pca9554RelayBackend (I2C expander, added with the S3 board),
// FakeRelayBackend (tests).
class RelayBackend {
 public:
  virtual ~RelayBackend() = default;

  // Initialize hardware (pin modes, expander config) and leave all relays
  // de-energized. This backend's own power-on write is the AUTHORITATIVE safe
  // state — e.g. Pca9554RelayBackend must write outputs 0x00 BEFORE switching the
  // expander to output mode (its POR default would otherwise energize relays).
  // ControllerRelayIo::begin() issues a redundant all-off write afterward; treat
  // that as an idempotent confirmation, not the safe-state guarantee.
  virtual void begin() = 0;

  // Drive the relays to exactly match `out`.
  virtual void write(const RelayDemand &out) = 0;
};

}  // namespace thermostat
