rgregg/esp32-wireless-thermostat/src/thermostat/thermostat_display_app.cpp

#include "thermostat/thermostat_display_app.h"

namespace thermostat {

ThermostatDisplayApp::ThermostatDisplayApp(ThermostatApp &thermostat_app)
    : app_(thermostat_app) {
  model_.set_local_setpoint_c(app_.local_setpoint_c());
}

void ThermostatDisplayApp::set_temperature_unit(TemperatureUnit unit) {
  model_.set_temperature_unit(unit);
}

void ThermostatDisplayApp::sync_from_app() {
  model_.set_local_setpoint_c(app_.local_setpoint_c());
}

void ThermostatDisplayApp::on_local_sensor_update(float indoor_temp_c,
                                                  float indoor_humidity) {
  const float compensated_temp_c = indoor_temp_c + local_temperature_compensation_c_;
  model_.set_local_indoor_temperature_c(compensated_temp_c);
  model_.set_local_indoor_humidity(indoor_humidity);
  app_.publish_indoor_temperature_c(compensated_temp_c);
  app_.publish_indoor_humidity(indoor_humidity);
}

void ThermostatDisplayApp::on_outdoor_weather_update(float outdoor_temp_c,
                                                     WeatherIcon icon) {
  model_.set_outdoor_temperature_c(outdoor_temp_c);
  model_.set_weather_icon(icon);
}

void ThermostatDisplayApp::on_controller_state_update(
    uint32_t now_ms, FurnaceStateCode state, bool lockout, FurnaceMode mode,
    FanMode fan, float setpoint_c, uint32_t filter_runtime_seconds,
    bool windows_open) {
  app_.on_controller_state_update(now_ms, state, lockout, mode, fan, setpoint_c,
                                  filter_runtime_seconds, windows_open);
  sync_from_app();
}

void ThermostatDisplayApp::on_user_set_setpoint(float user_value, uint32_t now_ms) {
  const float celsius = model_.to_celsius_from_user(user_value);
  app_.set_local_setpoint_c(celsius, now_ms);
  model_.set_local_setpoint_c(app_.local_setpoint_c());
}

void ThermostatDisplayApp::on_user_set_setpoint_c(float setpoint_c, uint32_t now_ms) {
  app_.set_local_setpoint_c(setpoint_c, now_ms);
  model_.set_local_setpoint_c(app_.local_setpoint_c());
}

void ThermostatDisplayApp::on_user_set_mode(FurnaceMode mode, uint32_t now_ms) {
  app_.set_local_mode(mode, now_ms);
}

void ThermostatDisplayApp::on_user_set_fan_mode(FanMode mode, uint32_t now_ms) {
  app_.set_local_fan_mode(mode, now_ms);
}

std::string ThermostatDisplayApp::status_text(uint32_t now_ms,
                                              uint32_t connection_timeout_ms) const {
  const bool connected = app_.controller_connected(now_ms, connection_timeout_ms);
  const bool has_tel = app_.has_controller_telemetry();
  const bool lockout = has_tel ? app_.controller_lockout() : false;
  const bool windows_open = has_tel ? app_.controller_windows_open() : false;
  const auto state =
      has_tel ? app_.controller_state() : FurnaceStateCode::Error;
  const FurnaceMode mode = app_.local_mode();
  return furnace_state_text(state, connected, lockout, /*failsafe_active=*/false,
                            windows_open, mode);
}

}  // namespace thermostat
