rgregg/esp32-wireless-thermostat/include/mqtt_payload.h

#pragma once

#include "thermostat_types.h"
#include <string.h>

namespace mqtt_payload {

// --- Mode/Fan enum <-> MQTT string ---

inline const char *mode_to_str(FurnaceMode mode) {
  switch (mode) {
    case FurnaceMode::Heat: return "heat";
    case FurnaceMode::Cool: return "cool";
    default: return "off";
  }
}

inline FurnaceMode str_to_mode(const char *s) {
  if (strcmp(s, "heat") == 0) return FurnaceMode::Heat;
  if (strcmp(s, "cool") == 0) return FurnaceMode::Cool;
  return FurnaceMode::Off;
}

inline const char *fan_to_str(FanMode mode) {
  switch (mode) {
    case FanMode::AlwaysOn: return "on";
    case FanMode::Circulate: return "circulate";
    default: return "auto";
  }
}

inline FanMode str_to_fan(const char *s) {
  if (strcmp(s, "on") == 0 || strcmp(s, "always on") == 0) return FanMode::AlwaysOn;
  if (strcmp(s, "circulate") == 0) return FanMode::Circulate;
  return FanMode::Automatic;
}

// --- Furnace state code to human-readable string ---

inline const char *furnace_state_to_str(FurnaceStateCode state) {
  switch (state) {
    case FurnaceStateCode::Idle: return "Idle";
    case FurnaceStateCode::HeatMode: return "Heat Standby";
    case FurnaceStateCode::HeatOn: return "Heating";
    case FurnaceStateCode::CoolMode: return "Cool Standby";
    case FurnaceStateCode::CoolOn: return "Cooling";
    case FurnaceStateCode::FanOn: return "Fan Running";
    case FurnaceStateCode::Error: return "Error";
    case FurnaceStateCode::HeatWait: return "Heat Wait";
    case FurnaceStateCode::CoolWait: return "Cool Wait";
    default: return "Unknown";
  }
}

inline FurnaceStateCode str_to_furnace_state(const char *s) {
  if (strcmp(s, "Idle") == 0)         return FurnaceStateCode::Idle;
  if (strcmp(s, "Heat Standby") == 0) return FurnaceStateCode::HeatMode;
  if (strcmp(s, "Heating") == 0)      return FurnaceStateCode::HeatOn;
  if (strcmp(s, "Cool Standby") == 0) return FurnaceStateCode::CoolMode;
  if (strcmp(s, "Cooling") == 0)      return FurnaceStateCode::CoolOn;
  if (strcmp(s, "Fan Running") == 0)  return FurnaceStateCode::FanOn;
  if (strcmp(s, "Heat Wait") == 0)    return FurnaceStateCode::HeatWait;
  if (strcmp(s, "Cool Wait") == 0)    return FurnaceStateCode::CoolWait;
  return FurnaceStateCode::Error;
}

// --- Bool payload parsing ---

inline bool parse_bool(const char *s) {
  if (s == nullptr) return false;
  return strcmp(s, "1") == 0 || strcmp(s, "true") == 0 || strcmp(s, "on") == 0;
}

}  // namespace mqtt_payload
