rgregg/esp32-wireless-thermostat/src/command_builder.cpp

#include "command_builder.h"

#include <math.h>

namespace thermostat {

CommandWord build_command_word(FurnaceMode mode,
                               FanMode fan,
                               float setpoint_c,
                               uint16_t seq,
                               bool sync_request,
                               bool filter_reset) {
  CommandWord cmd;
  cmd.mode = mode;
  cmd.fan = fan;

  if (!isfinite(setpoint_c)) {
    setpoint_c = 0.0f;
  }
  if (setpoint_c < 0.0f) {
    setpoint_c = 0.0f;
  }
  if (setpoint_c > 40.0f) {
    setpoint_c = 40.0f;
  }
  int setpoint_decic = static_cast<int>(setpoint_c * 10.0f + 0.5f);
  cmd.setpoint_decic = static_cast<uint16_t>(setpoint_decic);
  cmd.seq = seq & 0x1FFu;
  cmd.sync_request = sync_request;
  cmd.filter_reset = filter_reset;
  return cmd;
}

uint32_t build_packed_command(FurnaceMode mode,
                              FanMode fan,
                              float setpoint_c,
                              uint16_t seq,
                              bool sync_request,
                              bool filter_reset) {
  return espnow_cmd::encode(
      build_command_word(mode, fan, setpoint_c, seq, sync_request, filter_reset));
}

}  // namespace thermostat
