rgregg/esp32-wireless-thermostat/include/management_paths.h

#pragma once

#include <string>

namespace thermostat {
namespace management_paths {

bool parse_cfg_set_topic(const std::string &base_topic, const std::string &topic,
                         std::string *key_out);
bool parse_cfg_state_topic(const std::string &base_topic, const std::string &topic,
                           std::string *key_out);
bool parse_prefixed_form_key(const std::string &name, const std::string &prefix,
                             std::string *key_out);
bool is_secret_cfg_key(const std::string &key);

}  // namespace management_paths
}  // namespace thermostat
