rgregg/esp32-wireless-thermostat/src/tests/test_controller_runtime.cpp

#if defined(THERMOSTAT_RUN_TESTS)
#include "controller/controller_runtime.h"
#include "test_harness.h"

TEST_CASE(controller_runtime_failsafe_lockout) {
  thermostat::ControllerConfig cfg;
  cfg.failsafe_timeout_ms = 5000;
  cfg.min_idle_time_ms = 0;
  cfg.min_heating_off_time_ms = 0;
  cfg.min_heating_run_time_ms = 0;
  cfg.min_cooling_off_time_ms = 0;
  cfg.min_cooling_run_time_ms = 0;
  thermostat::ControllerRuntime rt(cfg);

  rt.note_heartbeat(1000);
  thermostat::ControllerTickInput t1;
  t1.now_ms = 2000;
  t1.cool_call = true;
  t1.has_indoor_temp = true;
  rt.tick(t1);
  ASSERT_TRUE(rt.cool_demand());

  thermostat::ControllerTickInput t2;
  t2.now_ms = 8000;
  t2.cool_call = true;
  t2.has_indoor_temp = true;
  rt.tick(t2);
  ASSERT_TRUE(rt.failsafe_active());
  ASSERT_TRUE(!rt.cool_demand());

  rt.note_heartbeat(9000);
  thermostat::ControllerTickInput t3;
  t3.now_ms = 9001;
  t3.has_indoor_temp = true;
  rt.tick(t3);
  ASSERT_TRUE(!rt.failsafe_active());

  rt.set_hvac_lockout(true);
  thermostat::ControllerTickInput t4;
  t4.now_ms = 9100;
  t4.heat_call = true;
  t4.has_indoor_temp = true;
  rt.tick(t4);
  ASSERT_TRUE(!rt.heat_demand());
}

TEST_CASE(controller_runtime_filter_runtime_and_circulate) {
  thermostat::ControllerConfig cfg;
  cfg.fan_circulate_period_min = 5;
  cfg.fan_circulate_duration_min = 2;
  cfg.min_idle_time_ms = 0;
  cfg.min_heating_off_time_ms = 0;
  cfg.min_heating_run_time_ms = 0;
  cfg.min_cooling_off_time_ms = 0;
  cfg.min_cooling_run_time_ms = 0;
  thermostat::ControllerRuntime rt(cfg);

  CommandWord cmd;
  cmd.fan = FanMode::Circulate;
  cmd.seq = 1;
  ASSERT_TRUE(rt.apply_remote_command(cmd).accepted);

  rt.note_heartbeat(1);
  thermostat::ControllerTickInput first;
  first.now_ms = 1000;
  first.has_indoor_temp = true;
  rt.tick(first);

  thermostat::ControllerTickInput second;
  second.now_ms = 61000;
  second.has_indoor_temp = true;
  rt.tick(second);

  ASSERT_TRUE(rt.fan_demand());
  thermostat::ControllerTickInput third;
  third.now_ms = 121000;
  third.has_indoor_temp = true;
  rt.tick(third);
  ASSERT_TRUE(rt.filter_runtime_seconds() >= 60);
}

TEST_CASE(controller_runtime_enforces_min_run_min_off_and_min_idle) {
  thermostat::ControllerConfig cfg;
  cfg.failsafe_timeout_ms = 1000000;
  cfg.min_idle_time_ms = 30000;
  cfg.min_heating_run_time_ms = 180000;
  cfg.min_heating_off_time_ms = 180000;
  cfg.min_cooling_run_time_ms = 300000;
  cfg.min_cooling_off_time_ms = 300000;
  thermostat::ControllerRuntime rt(cfg);

  rt.note_heartbeat(1);

  thermostat::ControllerTickInput t1;
  t1.now_ms = 1000;
  t1.heat_call = true;
  t1.has_indoor_temp = true;
  rt.tick(t1);
  ASSERT_TRUE(!rt.heat_demand());

  thermostat::ControllerTickInput t2;
  t2.now_ms = 31000;
  t2.heat_call = true;
  t2.has_indoor_temp = true;
  rt.tick(t2);
  ASSERT_TRUE(rt.heat_demand());

  thermostat::ControllerTickInput t3;
  t3.now_ms = 60000;
  t3.heat_call = false;
  t3.has_indoor_temp = true;
  rt.tick(t3);
  ASSERT_TRUE(rt.heat_demand());

  thermostat::ControllerTickInput t4;
  t4.now_ms = 211000;
  t4.heat_call = false;
  t4.has_indoor_temp = true;
  rt.tick(t4);
  ASSERT_TRUE(!rt.heat_demand());

  thermostat::ControllerTickInput t5;
  t5.now_ms = 220000;
  t5.heat_call = true;
  t5.has_indoor_temp = true;
  rt.tick(t5);
  ASSERT_TRUE(!rt.heat_demand());

  thermostat::ControllerTickInput t6;
  t6.now_ms = 392000;
  t6.heat_call = true;
  t6.has_indoor_temp = true;
  rt.tick(t6);
  ASSERT_TRUE(rt.heat_demand());
}

TEST_CASE(controller_runtime_failsafe_activates_without_indoor_temp) {
  thermostat::ControllerConfig cfg;
  cfg.failsafe_timeout_ms = 5000;
  cfg.min_idle_time_ms = 0;
  cfg.min_heating_off_time_ms = 0;
  cfg.min_heating_run_time_ms = 0;
  cfg.min_cooling_off_time_ms = 0;
  cfg.min_cooling_run_time_ms = 0;
  thermostat::ControllerRuntime rt(cfg);

  rt.note_heartbeat(1000);
  thermostat::ControllerTickInput t1;
  t1.now_ms = 2000;
  t1.heat_call = true;
  t1.has_indoor_temp = false;  // No sensor data
  rt.tick(t1);

  // Failsafe should activate immediately when there's no indoor temp,
  // regardless of heartbeat freshness
  ASSERT_TRUE(rt.failsafe_active());
  ASSERT_TRUE(!rt.heat_demand());
}

TEST_CASE(controller_runtime_reset_remote_command_sequence_allows_reseed) {
  thermostat::ControllerRuntime rt;

  CommandWord cmd;
  cmd.seq = 100;
  ASSERT_TRUE(rt.apply_remote_command(cmd).accepted);

  cmd.seq = 1;
  ASSERT_TRUE(rt.apply_remote_command(cmd).stale_or_duplicate);

  rt.reset_remote_command_sequence();
  ASSERT_TRUE(rt.apply_remote_command(cmd).accepted);
}

TEST_CASE(controller_runtime_per_source_sequence_tracking) {
  thermostat::ControllerRuntime rt;

  // Two different source MACs
  const uint8_t mac_a[6] = {0xAA, 0xBB, 0xCC, 0xDD, 0xEE, 0x01};
  const uint8_t mac_b[6] = {0xAA, 0xBB, 0xCC, 0xDD, 0xEE, 0x02};

  // Source A sends seq=1
  CommandWord cmd;
  cmd.seq = 1;
  cmd.mode = FurnaceMode::Heat;
  cmd.setpoint_decic = 210;
  ASSERT_TRUE(rt.apply_remote_command(cmd, mac_a).accepted);

  // Source B also sends seq=1 — should be accepted (independent sequence)
  cmd.seq = 1;
  cmd.mode = FurnaceMode::Cool;
  cmd.setpoint_decic = 240;
  ASSERT_TRUE(rt.apply_remote_command(cmd, mac_b).accepted);

  // Source A sends seq=2 — accepted
  cmd.seq = 2;
  ASSERT_TRUE(rt.apply_remote_command(cmd, mac_a).accepted);

  // Source A sends seq=1 again — stale
  cmd.seq = 1;
  ASSERT_TRUE(rt.apply_remote_command(cmd, mac_a).stale_or_duplicate);

  // Source B sends seq=2 — accepted
  cmd.seq = 2;
  ASSERT_TRUE(rt.apply_remote_command(cmd, mac_b).accepted);

  // Reset clears all sources
  rt.reset_remote_command_sequence();
  cmd.seq = 1;
  ASSERT_TRUE(rt.apply_remote_command(cmd, mac_a).accepted);
  cmd.seq = 1;
  ASSERT_TRUE(rt.apply_remote_command(cmd, mac_b).accepted);
}

TEST_CASE(controller_runtime_max_heating_runtime_forces_idle) {
  thermostat::ControllerConfig cfg;
  cfg.failsafe_timeout_ms = 1000000;
  cfg.min_idle_time_ms = 0;
  cfg.min_heating_off_time_ms = 0;
  cfg.min_heating_run_time_ms = 0;
  cfg.max_heating_run_time_ms = 60000;  // 60 seconds
  thermostat::ControllerRuntime rt(cfg);

  rt.note_heartbeat(1);

  // Start heating
  thermostat::ControllerTickInput t1;
  t1.now_ms = 1000;
  t1.heat_call = true;
  t1.has_indoor_temp = true;
  rt.tick(t1);
  ASSERT_TRUE(rt.heat_demand());
  ASSERT_TRUE(!rt.max_runtime_exceeded());

  // Still heating before max runtime
  thermostat::ControllerTickInput t2;
  t2.now_ms = 50000;
  t2.heat_call = true;
  t2.has_indoor_temp = true;
  rt.tick(t2);
  ASSERT_TRUE(rt.heat_demand());

  // Max runtime exceeded — forced idle even with heat_call
  thermostat::ControllerTickInput t3;
  t3.now_ms = 62000;
  t3.heat_call = true;
  t3.has_indoor_temp = true;
  rt.tick(t3);
  ASSERT_TRUE(!rt.heat_demand());
  ASSERT_TRUE(rt.max_runtime_exceeded());
}

TEST_CASE(controller_runtime_max_cooling_runtime_forces_idle) {
  thermostat::ControllerConfig cfg;
  cfg.failsafe_timeout_ms = 1000000;
  cfg.min_idle_time_ms = 0;
  cfg.min_cooling_off_time_ms = 0;
  cfg.min_cooling_run_time_ms = 0;
  cfg.max_cooling_run_time_ms = 60000;  // 60 seconds
  thermostat::ControllerRuntime rt(cfg);

  rt.note_heartbeat(1);

  // Start cooling
  thermostat::ControllerTickInput t1;
  t1.now_ms = 1000;
  t1.cool_call = true;
  t1.has_indoor_temp = true;
  rt.tick(t1);
  ASSERT_TRUE(rt.cool_demand());
  ASSERT_TRUE(!rt.max_runtime_exceeded());

  // Max runtime exceeded — forced idle even with cool_call
  thermostat::ControllerTickInput t2;
  t2.now_ms = 62000;
  t2.cool_call = true;
  t2.has_indoor_temp = true;
  rt.tick(t2);
  ASSERT_TRUE(!rt.cool_demand());
  ASSERT_TRUE(rt.max_runtime_exceeded());
}

TEST_CASE(controller_runtime_max_runtime_zero_disables_limit) {
  thermostat::ControllerConfig cfg;
  cfg.failsafe_timeout_ms = 100000000;  // large to avoid failsafe
  cfg.min_idle_time_ms = 0;
  cfg.min_heating_off_time_ms = 0;
  cfg.min_heating_run_time_ms = 0;
  cfg.max_heating_run_time_ms = 0;  // disabled
  cfg.max_cooling_run_time_ms = 0;  // disabled
  thermostat::ControllerRuntime rt(cfg);

  rt.note_heartbeat(1);

  // Start heating
  thermostat::ControllerTickInput t1;
  t1.now_ms = 1000;
  t1.heat_call = true;
  t1.has_indoor_temp = true;
  rt.tick(t1);
  ASSERT_TRUE(rt.heat_demand());

  // Way past any reasonable runtime — should still be heating
  thermostat::ControllerTickInput t2;
  t2.now_ms = 50000000;  // ~14 hours
  t2.heat_call = true;
  t2.has_indoor_temp = true;
  rt.tick(t2);
  ASSERT_TRUE(rt.heat_demand());
  ASSERT_TRUE(!rt.max_runtime_exceeded());
}

TEST_CASE(controller_runtime_max_runtime_allows_restart_after_off_time) {
  thermostat::ControllerConfig cfg;
  cfg.failsafe_timeout_ms = 1000000;
  cfg.min_idle_time_ms = 0;
  cfg.min_heating_off_time_ms = 30000;
  cfg.min_heating_run_time_ms = 0;
  cfg.max_heating_run_time_ms = 60000;
  thermostat::ControllerRuntime rt(cfg);

  rt.note_heartbeat(1);

  // Start heating
  thermostat::ControllerTickInput t1;
  t1.now_ms = 1000;
  t1.heat_call = true;
  t1.has_indoor_temp = true;
  rt.tick(t1);
  ASSERT_TRUE(rt.heat_demand());

  // Max runtime exceeded
  thermostat::ControllerTickInput t2;
  t2.now_ms = 62000;
  t2.heat_call = true;
  t2.has_indoor_temp = true;
  rt.tick(t2);
  ASSERT_TRUE(!rt.heat_demand());
  ASSERT_TRUE(rt.max_runtime_exceeded());

  // Try to restart immediately — blocked by min off time
  thermostat::ControllerTickInput t3;
  t3.now_ms = 63000;
  t3.heat_call = true;
  t3.has_indoor_temp = true;
  rt.tick(t3);
  ASSERT_TRUE(!rt.heat_demand());

  // After min off time elapses — restart allowed, flag cleared
  thermostat::ControllerTickInput t4;
  t4.now_ms = 93000;
  t4.heat_call = true;
  t4.has_indoor_temp = true;
  rt.tick(t4);
  ASSERT_TRUE(rt.heat_demand());
  ASSERT_TRUE(!rt.max_runtime_exceeded());
}

TEST_CASE(controller_runtime_normal_stop_does_not_set_max_runtime_flag) {
  thermostat::ControllerConfig cfg;
  cfg.failsafe_timeout_ms = 1000000;
  cfg.min_idle_time_ms = 0;
  cfg.min_heating_off_time_ms = 0;
  cfg.min_heating_run_time_ms = 0;
  cfg.max_heating_run_time_ms = 60000;
  thermostat::ControllerRuntime rt(cfg);

  rt.note_heartbeat(1);

  // Start heating
  thermostat::ControllerTickInput t1;
  t1.now_ms = 1000;
  t1.heat_call = true;
  t1.has_indoor_temp = true;
  rt.tick(t1);
  ASSERT_TRUE(rt.heat_demand());

  // Heat call drops before max runtime — normal stop
  thermostat::ControllerTickInput t2;
  t2.now_ms = 30000;
  t2.heat_call = false;
  t2.has_indoor_temp = true;
  rt.tick(t2);
  ASSERT_TRUE(!rt.heat_demand());
  ASSERT_TRUE(!rt.max_runtime_exceeded());
}

TEST_CASE(controller_runtime_max_runtime_flag_persists_in_idle) {
  thermostat::ControllerConfig cfg;
  cfg.failsafe_timeout_ms = 1000000;
  cfg.min_idle_time_ms = 0;
  cfg.min_heating_off_time_ms = 60000;
  cfg.min_heating_run_time_ms = 0;
  cfg.max_heating_run_time_ms = 60000;
  thermostat::ControllerRuntime rt(cfg);

  rt.note_heartbeat(1);

  // Start heating, then exceed max runtime
  thermostat::ControllerTickInput t1;
  t1.now_ms = 1000;
  t1.heat_call = true;
  t1.has_indoor_temp = true;
  rt.tick(t1);

  thermostat::ControllerTickInput t2;
  t2.now_ms = 62000;
  t2.heat_call = true;
  t2.has_indoor_temp = true;
  rt.tick(t2);
  ASSERT_TRUE(rt.max_runtime_exceeded());

  // Subsequent idle ticks — flag should persist
  thermostat::ControllerTickInput t3;
  t3.now_ms = 70000;
  t3.heat_call = true;
  t3.has_indoor_temp = true;
  rt.tick(t3);
  ASSERT_TRUE(!rt.heat_demand());
  ASSERT_TRUE(rt.max_runtime_exceeded());
}

TEST_CASE(controller_runtime_max_runtime_flag_clears_on_mode_change) {
  thermostat::ControllerConfig cfg;
  cfg.failsafe_timeout_ms = 1000000;
  cfg.min_idle_time_ms = 0;
  cfg.min_heating_off_time_ms = 0;
  cfg.min_heating_run_time_ms = 0;
  cfg.max_heating_run_time_ms = 60000;
  thermostat::ControllerRuntime rt(cfg);

  rt.note_heartbeat(1);

  // Start heating
  CommandWord cmd;
  cmd.seq = 1;
  cmd.mode = FurnaceMode::Heat;
  cmd.fan = FanMode::Automatic;
  cmd.setpoint_decic = 220;
  rt.apply_remote_command(cmd, nullptr);

  thermostat::ControllerTickInput t1;
  t1.now_ms = 1000;
  t1.heat_call = true;
  t1.has_indoor_temp = true;
  rt.tick(t1);

  // Exceed max runtime
  thermostat::ControllerTickInput t2;
  t2.now_ms = 62000;
  t2.heat_call = true;
  t2.has_indoor_temp = true;
  rt.tick(t2);
  ASSERT_TRUE(rt.max_runtime_exceeded());

  // User changes mode to Off — flag should clear
  CommandWord cmd2;
  cmd2.seq = 2;
  cmd2.mode = FurnaceMode::Off;
  cmd2.fan = FanMode::Automatic;
  cmd2.setpoint_decic = 220;
  rt.apply_remote_command(cmd2, nullptr);
  ASSERT_TRUE(!rt.max_runtime_exceeded());
}

TEST_CASE(controller_runtime_failsafe_during_heating_does_not_set_max_runtime_flag) {
  thermostat::ControllerConfig cfg;
  cfg.failsafe_timeout_ms = 5000;
  cfg.min_idle_time_ms = 0;
  cfg.min_heating_off_time_ms = 0;
  cfg.min_heating_run_time_ms = 0;
  cfg.max_heating_run_time_ms = 60000;
  thermostat::ControllerRuntime rt(cfg);

  rt.note_heartbeat(1000);

  // Start heating
  thermostat::ControllerTickInput t1;
  t1.now_ms = 2000;
  t1.heat_call = true;
  t1.has_indoor_temp = true;
  rt.tick(t1);
  ASSERT_TRUE(rt.heat_demand());

  // Failsafe triggers (heartbeat timeout) before max runtime
  thermostat::ControllerTickInput t2;
  t2.now_ms = 8000;
  t2.heat_call = true;
  t2.has_indoor_temp = true;
  rt.tick(t2);
  ASSERT_TRUE(rt.failsafe_active());
  ASSERT_TRUE(!rt.heat_demand());
  ASSERT_TRUE(!rt.max_runtime_exceeded());
}

TEST_CASE(controller_runtime_null_source_uses_default_sequence) {
  thermostat::ControllerRuntime rt;

  CommandWord cmd;
  cmd.seq = 5;
  ASSERT_TRUE(rt.apply_remote_command(cmd, nullptr).accepted);

  // Same seq without source — duplicate
  ASSERT_TRUE(rt.apply_remote_command(cmd, nullptr).stale_or_duplicate);

  // Different source MAC with same seq — accepted (independent)
  const uint8_t mac_a[6] = {0x11, 0x22, 0x33, 0x44, 0x55, 0x66};
  cmd.seq = 5;
  ASSERT_TRUE(rt.apply_remote_command(cmd, mac_a).accepted);
}

TEST_CASE(controller_runtime_display_mac_does_not_block_mqtt_commands) {
  // Regression: display's packed_command (with MAC) advancing seq should not
  // block direct MQTT cmd/* commands (nullptr source).
  thermostat::ControllerRuntime rt;

  const uint8_t display_mac[6] = {0xAA, 0xBB, 0xCC, 0xDD, 0xEE, 0xFF};

  // Display sends many commands, advancing its sequence far ahead
  CommandWord cmd;
  for (uint8_t i = 1; i <= 50; ++i) {
    cmd.seq = i;
    cmd.mode = FurnaceMode::Heat;
    cmd.setpoint_decic = 210;
    ASSERT_TRUE(rt.apply_remote_command(cmd, display_mac).accepted);
  }

  // Direct MQTT command with low seq via nullptr — must still be accepted
  cmd.seq = 1;
  cmd.mode = FurnaceMode::Cool;
  cmd.setpoint_decic = 240;
  ASSERT_TRUE(rt.apply_remote_command(cmd, nullptr).accepted);

  // Second direct MQTT command with seq=2 — also accepted
  cmd.seq = 2;
  ASSERT_TRUE(rt.apply_remote_command(cmd, nullptr).accepted);

  // But duplicate on nullptr is still rejected
  cmd.seq = 2;
  ASSERT_TRUE(rt.apply_remote_command(cmd, nullptr).stale_or_duplicate);
}

TEST_CASE(controller_runtime_per_mode_setpoints_preserved_across_mode_switch) {
  thermostat::ControllerRuntime rt;

  // Heat mode at 21.0°C
  CommandWord cmd;
  cmd.seq = 1;
  cmd.mode = FurnaceMode::Heat;
  cmd.setpoint_decic = 210;
  ASSERT_TRUE(rt.apply_remote_command(cmd).accepted);
  ASSERT_TRUE(rt.target_temperature_c() == 21.0f);
  ASSERT_TRUE(rt.heat_setpoint_c() == 21.0f);

  // Switch to cool at 23.5°C — heat bin must be preserved
  cmd.seq = 2;
  cmd.mode = FurnaceMode::Cool;
  cmd.setpoint_decic = 235;
  ASSERT_TRUE(rt.apply_remote_command(cmd).accepted);
  ASSERT_TRUE(rt.target_temperature_c() == 23.5f);
  ASSERT_TRUE(rt.cool_setpoint_c() == 23.5f);
  ASSERT_TRUE(rt.heat_setpoint_c() == 21.0f);

  // Switch back to heat with a stale-bin payload (e.g. 21.0) — cool bin preserved
  cmd.seq = 3;
  cmd.mode = FurnaceMode::Heat;
  cmd.setpoint_decic = 210;
  ASSERT_TRUE(rt.apply_remote_command(cmd).accepted);
  ASSERT_TRUE(rt.target_temperature_c() == 21.0f);
  ASSERT_TRUE(rt.cool_setpoint_c() == 23.5f);
}

TEST_CASE(controller_runtime_preserve_setpoint_keeps_bins_intact) {
  thermostat::ControllerRuntime rt;

  // Seed both bins via two normal commands.
  CommandWord cmd;
  cmd.seq = 1;
  cmd.mode = FurnaceMode::Heat;
  cmd.setpoint_decic = 215;
  rt.apply_remote_command(cmd);
  cmd.seq = 2;
  cmd.mode = FurnaceMode::Cool;
  cmd.setpoint_decic = 240;
  rt.apply_remote_command(cmd);

  // A "mode-only" command from a smart sender carries an arbitrary setpoint
  // payload but flags preserve_setpoint=true. Bins must not change.
  cmd.seq = 3;
  cmd.mode = FurnaceMode::Heat;
  cmd.setpoint_decic = 999;
  cmd.preserve_setpoint = true;
  ASSERT_TRUE(rt.apply_remote_command(cmd).accepted);
  ASSERT_TRUE(rt.heat_setpoint_c() == 21.5f);
  ASSERT_TRUE(rt.cool_setpoint_c() == 24.0f);
  ASSERT_EQ(static_cast<int>(rt.mode()), static_cast<int>(FurnaceMode::Heat));
}

TEST_CASE(controller_runtime_preserve_mode_keeps_mode_intact) {
  thermostat::ControllerRuntime rt;

  CommandWord cmd;
  cmd.seq = 1;
  cmd.mode = FurnaceMode::Heat;
  cmd.setpoint_decic = 210;
  rt.apply_remote_command(cmd);

  // Setpoint-only update: preserve_mode=true keeps Heat. Setpoint routes by
  // resolved mode (Heat), so heat_bin updates and cool_bin is untouched.
  cmd.seq = 2;
  cmd.mode = FurnaceMode::Heat;
  cmd.setpoint_decic = 215;
  cmd.preserve_mode = true;
  cmd.preserve_setpoint = false;
  ASSERT_TRUE(rt.apply_remote_command(cmd).accepted);
  ASSERT_EQ(static_cast<int>(rt.mode()), static_cast<int>(FurnaceMode::Heat));
  ASSERT_TRUE(rt.heat_setpoint_c() == 21.5f);
  ASSERT_TRUE(rt.cool_setpoint_c() == 24.0f);
}

TEST_CASE(controller_runtime_off_mode_does_not_overwrite_setpoints) {
  thermostat::ControllerRuntime rt;

  CommandWord cmd;
  cmd.seq = 1;
  cmd.mode = FurnaceMode::Heat;
  cmd.setpoint_decic = 215;
  rt.apply_remote_command(cmd);

  cmd.seq = 2;
  cmd.mode = FurnaceMode::Cool;
  cmd.setpoint_decic = 240;
  rt.apply_remote_command(cmd);

  // Mode=Off with arbitrary setpoint payload must leave both bins intact.
  cmd.seq = 3;
  cmd.mode = FurnaceMode::Off;
  cmd.setpoint_decic = 100;
  ASSERT_TRUE(rt.apply_remote_command(cmd).accepted);
  ASSERT_TRUE(rt.heat_setpoint_c() == 21.5f);
  ASSERT_TRUE(rt.cool_setpoint_c() == 24.0f);
}

TEST_CASE(controller_runtime_windows_open_suppresses_cooling) {
  thermostat::ControllerConfig cfg;
  cfg.failsafe_timeout_ms = 1000000;
  cfg.min_idle_time_ms = 0;
  cfg.min_cooling_off_time_ms = 0;
  cfg.min_cooling_run_time_ms = 0;
  thermostat::ControllerRuntime rt(cfg);
  rt.note_heartbeat(1);

  CommandWord cmd;
  cmd.mode = FurnaceMode::Cool;
  cmd.seq = 1;
  ASSERT_TRUE(rt.apply_remote_command(cmd).accepted);

  thermostat::ControllerTickInput t1;
  t1.now_ms = 1000;
  t1.cool_call = true;
  t1.has_indoor_temp = true;
  rt.tick(t1);
  ASSERT_TRUE(rt.cool_demand());

  ASSERT_TRUE(!rt.snapshot().windows_open);

  rt.set_windows_open(true);
  thermostat::ControllerTickInput t2;
  t2.now_ms = 2000;
  t2.cool_call = true;
  t2.has_indoor_temp = true;
  rt.tick(t2);
  ASSERT_TRUE(rt.windows_open());
  ASSERT_TRUE(rt.snapshot().windows_open);
  ASSERT_TRUE(!rt.cool_demand());

  rt.set_windows_open(false);
  thermostat::ControllerTickInput t3;
  t3.now_ms = 3000;
  t3.cool_call = true;
  t3.has_indoor_temp = true;
  rt.tick(t3);
  ASSERT_TRUE(rt.cool_demand());
}

TEST_CASE(controller_runtime_windows_open_does_not_block_heat) {
  thermostat::ControllerConfig cfg;
  cfg.failsafe_timeout_ms = 1000000;
  cfg.min_idle_time_ms = 0;
  cfg.min_heating_off_time_ms = 0;
  cfg.min_heating_run_time_ms = 0;
  thermostat::ControllerRuntime rt(cfg);
  rt.note_heartbeat(1);

  CommandWord cmd;
  cmd.mode = FurnaceMode::Heat;
  cmd.seq = 1;
  ASSERT_TRUE(rt.apply_remote_command(cmd).accepted);

  rt.set_windows_open(true);
  thermostat::ControllerTickInput t1;
  t1.now_ms = 1000;
  t1.heat_call = true;
  t1.has_indoor_temp = true;
  rt.tick(t1);
  ASSERT_TRUE(rt.heat_demand());
}

TEST_CASE(controller_runtime_windows_open_honors_cool_min_run_time) {
  thermostat::ControllerConfig cfg;
  cfg.failsafe_timeout_ms = 1000000;
  cfg.min_idle_time_ms = 0;
  cfg.min_cooling_off_time_ms = 0;
  cfg.min_cooling_run_time_ms = 60000;
  thermostat::ControllerRuntime rt(cfg);
  rt.note_heartbeat(1);

  CommandWord cmd;
  cmd.mode = FurnaceMode::Cool;
  cmd.seq = 1;
  ASSERT_TRUE(rt.apply_remote_command(cmd).accepted);

  thermostat::ControllerTickInput t1;
  t1.now_ms = 1000;
  t1.cool_call = true;
  t1.has_indoor_temp = true;
  rt.tick(t1);
  ASSERT_TRUE(rt.cool_demand());

  rt.set_windows_open(true);
  thermostat::ControllerTickInput t2;
  t2.now_ms = 30000;
  t2.cool_call = true;
  t2.has_indoor_temp = true;
  rt.tick(t2);
  ASSERT_TRUE(rt.cool_demand());

  thermostat::ControllerTickInput t3;
  t3.now_ms = 70000;
  t3.cool_call = true;
  t3.has_indoor_temp = true;
  rt.tick(t3);
  ASSERT_TRUE(!rt.cool_demand());
}

TEST_CASE(controller_runtime_windows_open_blocks_cooling_re_entry_after_min_off) {
  // After cooling idles, windows_open must prevent re-entry regardless of elapsed time.
  thermostat::ControllerConfig cfg;
  cfg.failsafe_timeout_ms = 1000000;
  cfg.min_idle_time_ms = 0;
  cfg.min_cooling_off_time_ms = 0;  // zero so only windows_open gates re-entry
  cfg.min_cooling_run_time_ms = 0;
  thermostat::ControllerRuntime rt(cfg);
  rt.note_heartbeat(1);

  CommandWord cmd;
  cmd.mode = FurnaceMode::Cool;
  cmd.seq = 1;
  ASSERT_TRUE(rt.apply_remote_command(cmd).accepted);

  // Start cooling
  thermostat::ControllerTickInput t1;
  t1.now_ms = 1000;
  t1.cool_call = true;
  t1.has_indoor_temp = true;
  rt.tick(t1);
  ASSERT_TRUE(rt.cool_demand());

  // Set windows open — cooling stops on the next tick
  rt.set_windows_open(true);
  thermostat::ControllerTickInput t2;
  t2.now_ms = 2000;
  t2.cool_call = false;
  t2.has_indoor_temp = true;
  rt.tick(t2);
  ASSERT_TRUE(!rt.cool_demand());

  // Plenty of time has passed (min-off-time is 0), but windows are still open
  // — re-entry must be refused
  thermostat::ControllerTickInput t3;
  t3.now_ms = 999000;
  t3.cool_call = true;
  t3.has_indoor_temp = true;
  rt.tick(t3);
  ASSERT_TRUE(rt.windows_open());
  ASSERT_TRUE(!rt.cool_demand());
}

TEST_CASE(controller_runtime_windows_open_fan_circulate_continues_in_cool_mode) {
  // Fan-circulate must still trigger on schedule even when windows_open=true
  // in Cool mode (windows_open only suppresses the compressor, not the fan).
  thermostat::ControllerConfig cfg;
  cfg.fan_circulate_period_min = 5;
  cfg.fan_circulate_duration_min = 2;
  cfg.min_idle_time_ms = 0;
  cfg.min_cooling_off_time_ms = 0;
  cfg.min_cooling_run_time_ms = 0;
  thermostat::ControllerRuntime rt(cfg);

  // Set Cool mode with Circulate fan
  CommandWord cmd;
  cmd.mode = FurnaceMode::Cool;
  cmd.fan = FanMode::Circulate;
  cmd.seq = 1;
  ASSERT_TRUE(rt.apply_remote_command(cmd).accepted);

  rt.set_windows_open(true);
  rt.note_heartbeat(1);

  // First tick — circulate period not reached yet
  thermostat::ControllerTickInput t1;
  t1.now_ms = 1000;
  t1.cool_call = false;  // no cool demand (windows open)
  t1.has_indoor_temp = true;
  rt.tick(t1);

  // Advance past circulate period (5 min = 300 s, period starts from first tick)
  thermostat::ControllerTickInput t2;
  t2.now_ms = 61000;  // matches the existing circulate test timing
  t2.cool_call = false;
  t2.has_indoor_temp = true;
  rt.tick(t2);

  // Fan should be circulating despite windows_open and despite no cool_demand
  ASSERT_TRUE(rt.fan_demand());
  // Cool demand must remain suppressed
  ASSERT_TRUE(!rt.cool_demand());
}
#endif
