rgregg/esp32-wireless-thermostat/src/tests/test_device_registry.cpp

#if defined(THERMOSTAT_RUN_TESTS)
#include <cstdint>
#include "device_registry.h"
#include "discovery_topics.h"
#include "test_harness.h"

// ── DeviceRegistry: upsert with timestamp ──

TEST_CASE(device_registry_upsert_sets_last_seen) {
  DeviceRegistry reg;
  ASSERT_TRUE(reg.upsert("AA:BB:CC:DD:EE:FF", "dev1", "controller", "1.2.3.4", 1000));
  ASSERT_EQ(reg.entries[0].last_seen_ms, static_cast<uint32_t>(1000));
}

TEST_CASE(device_registry_upsert_updates_last_seen) {
  DeviceRegistry reg;
  reg.upsert("AA:BB:CC:DD:EE:FF", "dev1", "controller", "1.2.3.4", 1000);
  reg.upsert("AA:BB:CC:DD:EE:FF", "dev1", "controller", "1.2.3.4", 5000);
  ASSERT_EQ(reg.entries[0].last_seen_ms, static_cast<uint32_t>(5000));
}

// ── DeviceRegistry: touch ──

TEST_CASE(device_registry_touch_updates_timestamp) {
  DeviceRegistry reg;
  reg.upsert("AA:BB:CC:DD:EE:FF", "dev1", "display", "1.2.3.4", 1000);
  ASSERT_TRUE(reg.touch("AA:BB:CC:DD:EE:FF", 9000));
  ASSERT_EQ(reg.entries[0].last_seen_ms, static_cast<uint32_t>(9000));
}

TEST_CASE(device_registry_touch_returns_false_for_unknown_mac) {
  DeviceRegistry reg;
  ASSERT_TRUE(!reg.touch("11:22:33:44:55:66", 1000));
}

TEST_CASE(device_registry_touch_does_not_change_other_fields) {
  DeviceRegistry reg;
  reg.upsert("AA:BB:CC:DD:EE:FF", "my_device", "controller", "10.0.0.1", 100);
  reg.touch("AA:BB:CC:DD:EE:FF", 5000);
  ASSERT_STR_EQ(reg.entries[0].name, "my_device");
  ASSERT_STR_EQ(reg.entries[0].type, "controller");
  ASSERT_STR_EQ(reg.entries[0].ip, "10.0.0.1");
}

// ── DeviceRegistry: remove ──

TEST_CASE(device_registry_remove_clears_entry) {
  DeviceRegistry reg;
  reg.upsert("AA:BB:CC:DD:EE:FF", "dev1", "controller", "1.2.3.4", 1000);
  ASSERT_EQ(reg.count(), static_cast<size_t>(1));
  ASSERT_TRUE(reg.remove("AA:BB:CC:DD:EE:FF"));
  ASSERT_EQ(reg.count(), static_cast<size_t>(0));
  ASSERT_TRUE(!reg.entries[0].occupied);
}

TEST_CASE(device_registry_remove_returns_false_for_unknown) {
  DeviceRegistry reg;
  ASSERT_TRUE(!reg.remove("11:22:33:44:55:66"));
}

TEST_CASE(device_registry_remove_frees_slot_for_reuse) {
  DeviceRegistry reg;
  reg.upsert("AA:BB:CC:DD:EE:FF", "dev1", "controller", "1.2.3.4", 1000);
  reg.remove("AA:BB:CC:DD:EE:FF");
  ASSERT_TRUE(reg.upsert("11:22:33:44:55:66", "dev2", "display", "5.6.7.8", 2000));
  ASSERT_EQ(reg.count(), static_cast<size_t>(1));
  ASSERT_STR_EQ(reg.entries[0].mac, "11:22:33:44:55:66");
}

// ── DeviceRegistry: is_stale ──

TEST_CASE(device_registry_is_stale_true_when_expired) {
  DeviceRegistry reg;
  reg.upsert("AA:BB:CC:DD:EE:FF", "dev1", "controller", "1.2.3.4", 1000);
  // 8 days later
  uint32_t now = 1000 + 8UL * 24 * 60 * 60 * 1000;
  uint32_t max_age = 7UL * 24 * 60 * 60 * 1000;
  ASSERT_TRUE(reg.is_stale(0, now, max_age));
}

TEST_CASE(device_registry_is_stale_false_when_fresh) {
  DeviceRegistry reg;
  reg.upsert("AA:BB:CC:DD:EE:FF", "dev1", "controller", "1.2.3.4", 1000);
  uint32_t now = 1000 + 3600000;  // 1 hour later
  uint32_t max_age = 7UL * 24 * 60 * 60 * 1000;
  ASSERT_TRUE(!reg.is_stale(0, now, max_age));
}

TEST_CASE(device_registry_is_stale_false_for_empty_slot) {
  DeviceRegistry reg;
  uint32_t max_age = 7UL * 24 * 60 * 60 * 1000;
  ASSERT_TRUE(!reg.is_stale(0, 999999999, max_age));
}
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
